Sphinkie/Radial-V/External Hardware/Carte Sparkfun FM/README.md

SparkFun FM Tuner Basic Breakout - Si4703
========================================

SparkFun FM Tuner Basic Breakout - Si4703

[*SparkFun FM Tuner Basic Breakout - Si4703 (BOB-11083)*](https://www.sparkfun.com/products/11083)

This breakout for the Silicon Laboratories Si4703 FM tuner chip is a little more stripped down than our FM Tuner Evaluation Board. 
 If your project already has an amplifier and just needs a full-featured FM tuner, this is the board for you. 

Repository Contents
-------------------

* **/SparkFunSi4703Demo**- Example code (no library required)
* **/Hardware** - Eagle design files (.brd, .sch)
* **/Libraries** - Libraries for use with the shield
* **/Production** - Production panel files (.brd)

Documentation
--------------
* **[Library](https://github.com/sparkfun/SparkFun_Si4703_Arduino_Library)** - Arduino library for the Si4703.
* **[SparkFun Fritzing repo](https://github.com/sparkfun/Fritzing_Parts)** - Fritzing diagrams for Sparkfun products.
* **[SparkFun 3D Model repo](https://github.com/sparkfun/3D_Models)** - 3D models of Sparkfun products. 

| **L OUT** | **R OUT** | **GND** | **VCC** | **SDIO** | **SCLK** | **SEN\*** | **RST\*** | **GPIO1** | **GPIO2** |
| --- | --- | --- | --- | --- | --- | --- | --- | --- | --- |
| audio | audio | ground  | 3,3 volts | bus I2C  | bus I2C  | N/U | Reset | N/U | info STC  |

License Information
-------------------

This product is _**open source**_! 

The **hardware** is released under [Creative Commons ShareAlike 4.0 International](https://creativecommons.org/licenses/by-sa/4.0/).

The **code** is beerware; if you see me (or any other SparkFun employee) at the local, and you've found our code helpful, please buy us a round!

Please use, reuse, and modify these files as you see fit. Please maintain attribution to SparkFun Electronics and release anything derivative under the same license.

Distributed as-is; no warranty is given.

- Your friends at SparkFun.
