Sphinkie/Radial-V/External Hardware/Carte ecran TFT/readme.md

# Arduino LCD Screen  (RETIRED)

## Overview

The Arduino TFT screen is a backlit LCD screen with headers. You can draw text, images, and shapes to the screen with the [TFT library](https://www.arduino.cc/en/Reference/TFTLibrary). There is an onboard micro-SD card slot on the back of the screen that  can, among other things, store bitmap images for the screen to display.

The screen's headers are designed to fit into the socket of any AVR-based Arduino (Uno, Leonardo, etc) or with the Arduino Due, Esplora, and Robot. To connect the screen to  other Arduino boards, read the tutorial on this [link](http://arduino.cc/en/Guide/TFTtoBoards).

## Hardware

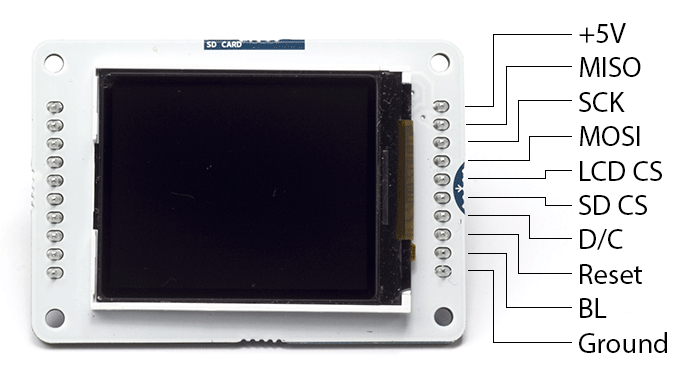
[picture p15: External Hardware/Carte ecran TFT/GLCD_pins.png]
GLCD_pins


The screen is 1.77" diagonal, with 160 x 128 pixel resolution. The  TFT library interfaces with the screen's controller through SPI when  using the [TFT library](https://www.arduino.cc/en/Reference/TFTLibrary). Refer to the [screen's data sheet](https://www.arduino.cc/en/uploads/Main/HTF0177SN-01-SPEC.pdf) for complete details.

- The screen runs on +5 VDC
- The micro-SD slot is accessible through the [SD card library](https://www.arduino.cc/en/Reference/SD).
- The LED backlight is dimmable by PWM.

## Library

The Arduino TFT library extends the [Adafruit GFX](https://github.com/adafruit/Adafruit-GFX-Library), and [Adafruit ST7735 libraries](https://github.com/adafruit/Adafruit-ST7735-Library) that it is based on. The GFX library is responsible for the drawing  routines, while the ST7735 library is specific to the screen on the  Arduino screen. The Arduino specific additions were designed to work as  similarly to the Processing API as possible.

The library is backwards compatible, which means you can still use the Adafruit functions [described here](http://learn.adafruit.com/adafruit-gfx-graphics-library/overview).

The TFT library relies on the [SPI library](https://www.arduino.cc/en/Reference/SPI), which must be included in any sketch that uses the screen.

If you wish to use the SD card, you need to include the [SD library](https://www.arduino.cc/en/Reference/SD) as well.

### Need Help?

- On the Software [on the Arduino Forum](https://forum.arduino.cc/index.php?board=63.0)

- On Projects [on the Arduino Forum](https://forum.arduino.cc/index.php?board=3.0)

- On the Product itself through [our Customer Support](https://store.arduino.cc/index.php?main_page=contact_us&language=en)

- Product Ref Code: A000096

  ## 

##
