Sphinkie/Radial-V/Hardware/Radial-V Bus/readme.md

# Radial-V

## Carte "Bus-Board"

Cette carte rassemble toutes les pins d'entrées/sorties utilisées de l'Arduino, vers une nappe 25 points, qui conduit à la carte "Extension Board". On plugge aussi dessus la carte "Sparkfun MP3 Player".

| Top View |  Bottom View |
| --- | --- |
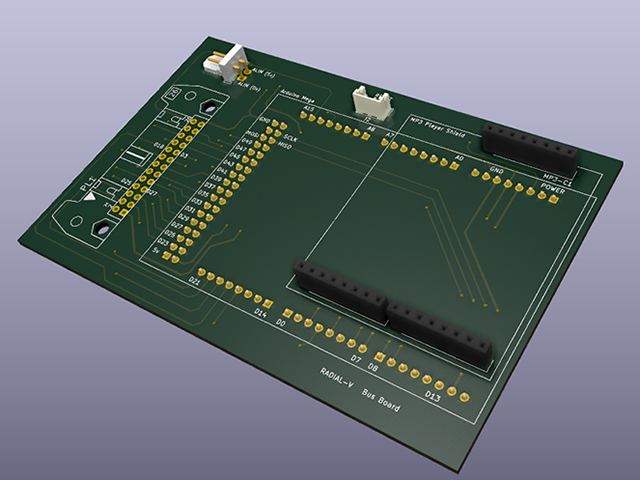
[picture p16: Hardware/Radial-V Bus/Radial-V_BusBoard-Top.png]
Radial-V Bus Board
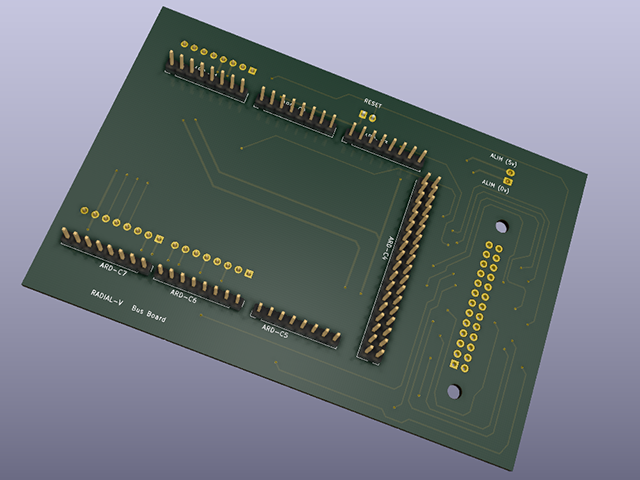
[picture p17: Hardware/Radial-V Bus/Radial-V_BusBoard-Bottom.png]
Radial-V Bus Board
|  |  |

### Schéma d'implémentation

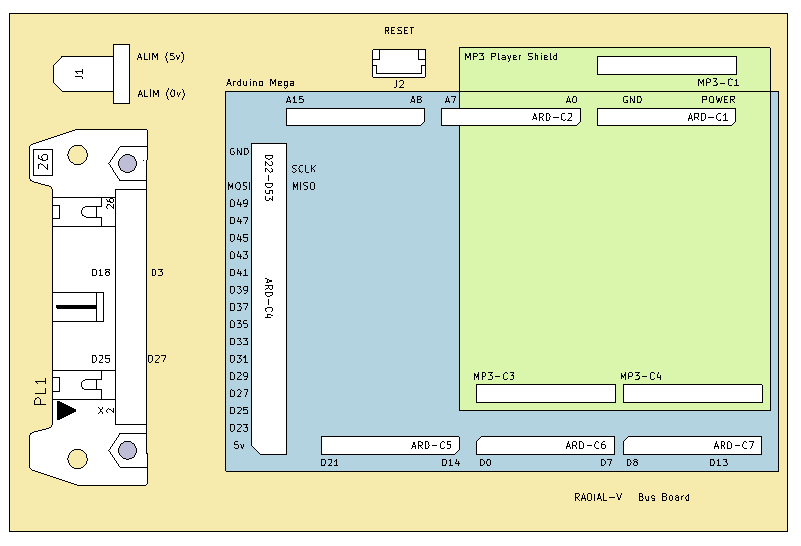
[picture p18: Hardware/Radial-V Bus/Radial-V_BusBoard-Silk.png]
Radial-V Bus Board
