Sphinkie/Radial-V/External Hardware/Carte Arduino Mega/readme.md

# RADIAL-V

## Cartes Arduino Mega

Radial-V comporte deux cartes Arduino Mega.

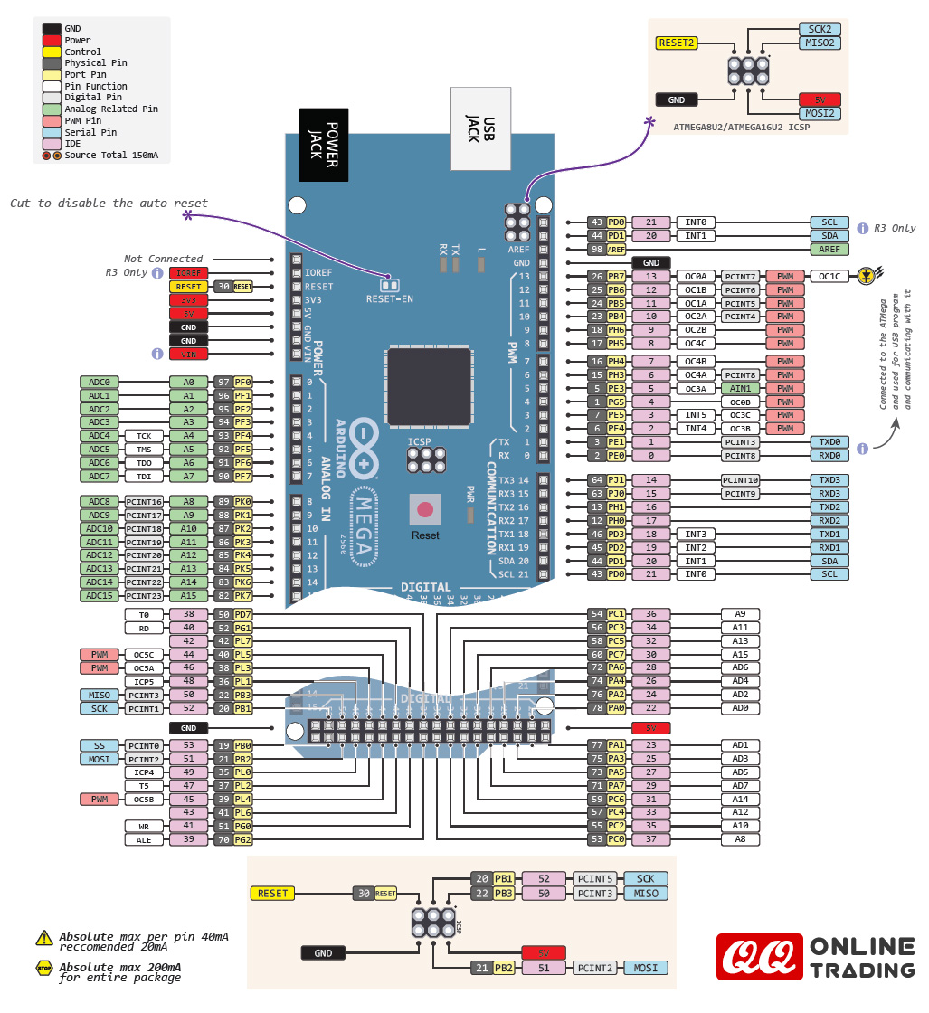
[picture p19: External Hardware/Carte Arduino Mega/Arduino_Mega_2560_Pinout.png]
Usefull Pinout


Le repository contient la documentation technique du constructeur.
