Sphinkie/Radial-V/3D objects/Boitiers/readme.md

# Radial-V

## Boîtiers

### Boîtier pour Bus Board

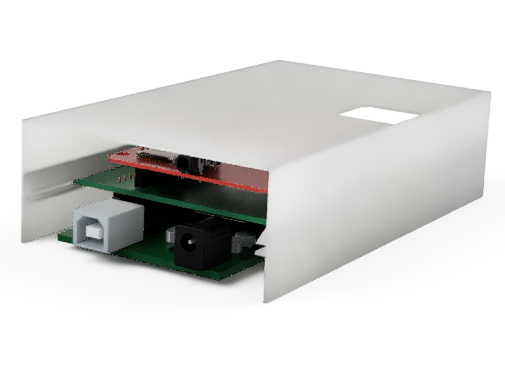
[picture p20: 3D objects/Boitiers/Couvercle_pour_Bus_Board.png]
Couvercle pour Bus Board


-----

### Boîtier pour Adaptateur Audio

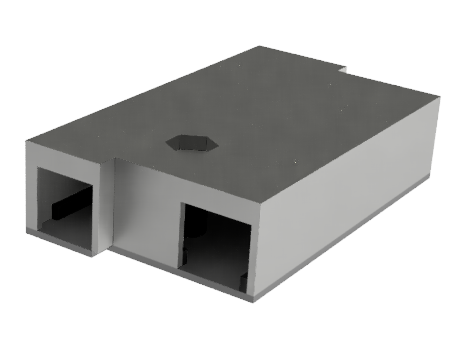
[picture p21: 3D objects/Boitiers/Boitier_Adaptateur_Audio.png]
Boitier_Adaptateur_Audio


---
