Sphinkie/Radial-V/3D objects/Support for TFT Screen Board/readme.md

# RADIAL-V

## Support pour écran TFT

Ce support permet de fixer le petit écran TFT sur le coté de la Radial-V.

[Vue du modèle 3D](Support%20for%20LCD.stl)

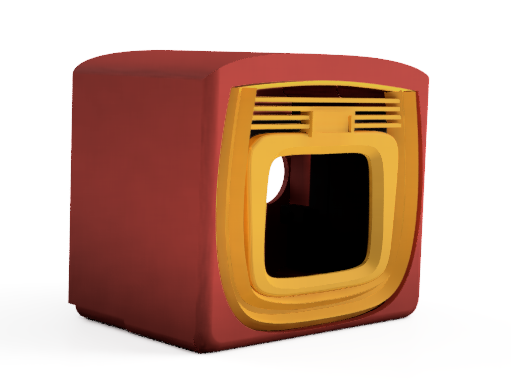
[picture p22: 3D objects/Support for TFT Screen Board/Support for LCD.png]
Vue de l'objet


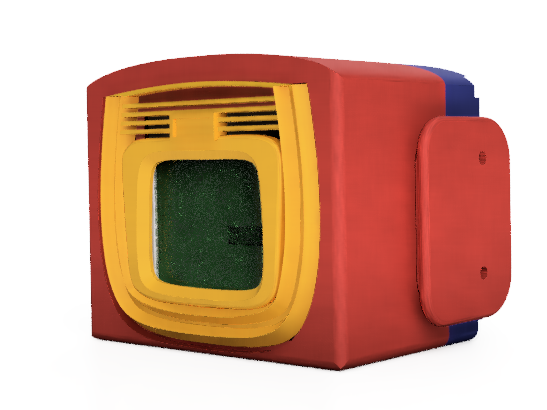
[picture p23: 3D objects/Support for TFT Screen Board/TFT_box-front.png]
TFT Box : front view


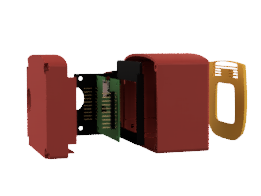
[picture p24: 3D objects/Support for TFT Screen Board/TFT_box-side.png]
TFT Box: side view
Side View:

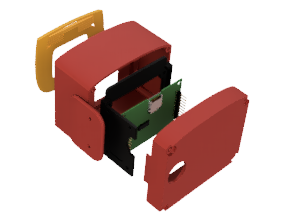
[picture p25: 3D objects/Support for TFT Screen Board/TFT_box-top.png]
TFT Box: top view
Top View:
