Sphinkie/Radial-V/3D objects/Support for Arduino Boards/readme.md

# RADIAL-V
## Supports

Ces supports permettent de rigidifier les plaques qui supportent les Arduino.
Elles se placent à chaque angle de ces plaques.

[Vue du modèle 3D](files/Radial-V%20Angles%20%28barre%20ARD1%29.stl)
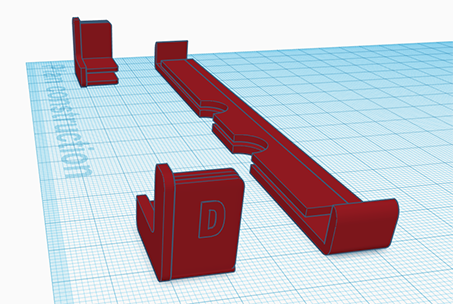
[picture p26: 3D objects/Support for Arduino Boards/images/Radial-V Angles (ARD1).png]
Exemple
