Sphinkie/Radial-V/3D objects/Support for LED/readme.md

# RADIAL-V
## Support for LED

La LED de l'activité de la carte SD a besoin d'un petit système de fixation pour se greffer au Radial-V.

[Vue du modèle 3D](Radial-V-Fixation-LED.stl)

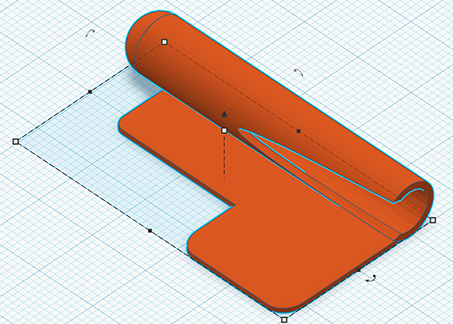
[picture p27: 3D objects/Support for LED/Radial-V-Fixation-LED.png]
Vue de l'objet
