Sphinkie/Radial-V/3D objects/Support for Extension Board/readme.md

# RADIAL-V

## Support for Extension Board

Ce support permet de fixer la carte d'extension **Ext. Board** au chassis du Radial-V.

[Vue du modèle 3D](Support_pour_Extension_Board.stl)

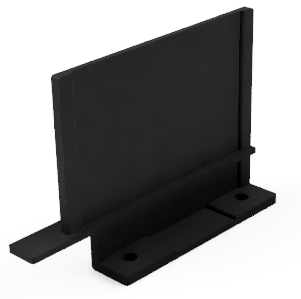
[picture p28: 3D objects/Support for Extension Board/Support_pour_Extension_Board.png]
Support_pour_Extension_Board
