Sphinkie/Radial-V/3D objects/Support for LCD Board/readme.md

# RADIAL-V

## Support pour LCD Board

Ce support permet de fixer le petit éran LCD sur le coté de la Radial-V.

[Vue du modèle 3D](Support%20for%20LCD.stl)

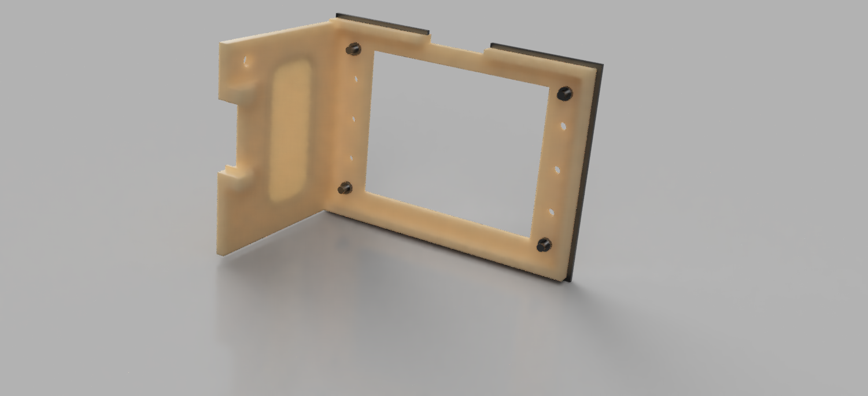
[picture p29: 3D objects/Support for LCD Board/Support for LCD.png]
Vue de l'objet
