Sphinkie/Radial-V/3D objects/Support for Alim Board/readme.md

# RADIAL-V
## Support pour la carte Alimentation

Support pour fixer la carte **Alim board** au chassis Radial-V.

[Vue du modèle 3D](Radial-V-ALIM.BOARD-Support.stl)

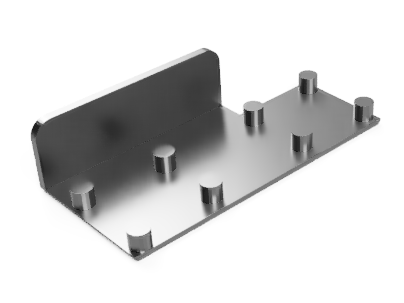
[picture p30: 3D objects/Support for Alim Board/Radial-V-ALIM.BOARD-Support_Naked.png]
Vue du support nu


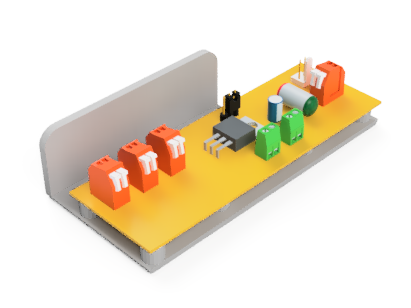
[picture p31: 3D objects/Support for Alim Board/Radial-V-ALIM.BOARD-Support_Boarded.png]
Vue du support avec la carte
