Sphinkie/Radial-V/3D objects/Support for Audio Board/readme.md

# RADIAL-V
## Support pour la carte Audio

Support pour fixer la carte **Audio Board** au chassis Radial-V.

[Vue du modèle 3D](Support%20Audio%20Board.stl)

Vue du support nu:

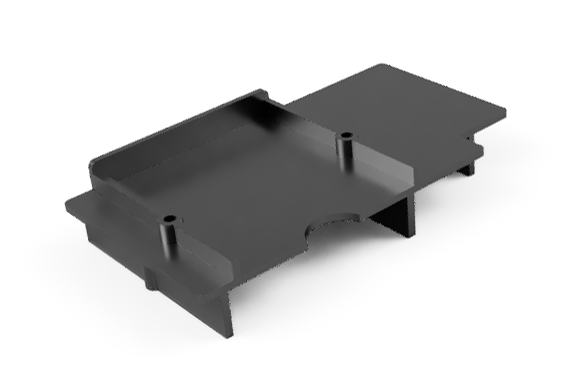
[picture p32: 3D objects/Support for Audio Board/Support_Audio_Board_naked.png]
Vue du support nu


Vue du support avec les cartes:

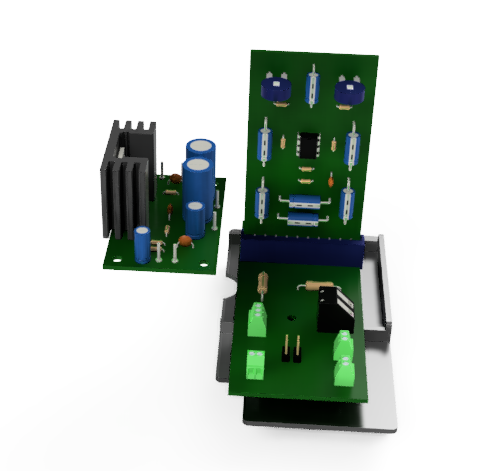
[picture p33: 3D objects/Support for Audio Board/Support_Audio_Board_boarded.png]
Vue du support avec les cartes
