Sphinkie/Radial-V/Hardware/Radial-V Audio board/3D Model/readme.md

# RADIAL-V
## Audio Board

Cette carte fait passer le signal audio par le potentiomètre de volume et l’amplificateur.

*Un slot est prévu pour un préamplificateur, qui au final ne s'est pas avéré nécessaire.*

[Vue du modèle 3D](Radial-V-Audio-Board.stl)

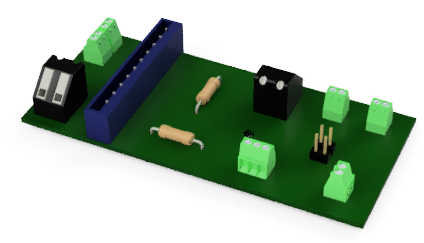
[picture p34: Hardware/Radial-V Audio board/3D Model/Radial-V-Audio-Board.png]
Vue de la carte
