Sphinkie/Radial-V/Hardware/Radial-V Extension board/3D Model/readme.md

# RADIAL-V
## Extension Board

Cette carte comporte des connecteurs d’entrée/sortie pour les différents capteurs de l’Arduino (boutons, Leds, ...)  avec leurs adaptations, et pilote les relais pour la sélection de l'audio (audio issue de la carte MP3 ou de la carte Radio-FM).

[Vue du modèle 3D](Radial-V%20Extension%20Board.stl)

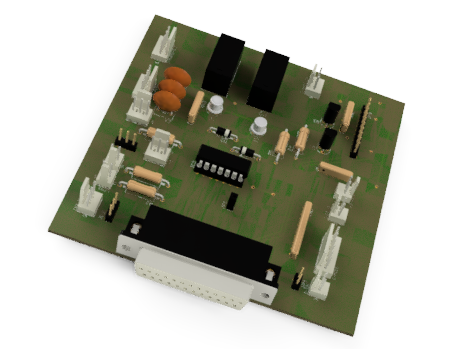
[picture p35: Hardware/Radial-V Extension board/3D Model/Radial-V_Extension_Board.png]
Vue de la carte
