Sphinkie/Radial-V/External Hardware/Carte ecran TFT/3D Model/readme.md

# RADIAL-V

## Arduino LCD Board

LCD screen with SD card for information display.

[Vue du modele 3D](Arduino_LCD_Board.stl)

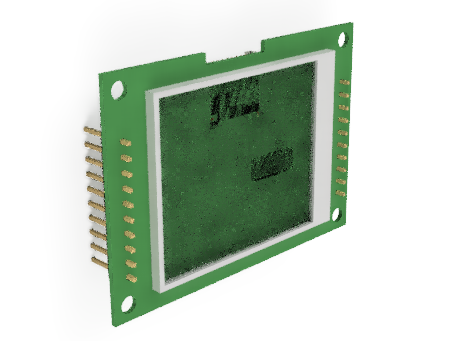
[picture p36: External Hardware/Carte ecran TFT/3D Model/Arduino_LCD_Board.png]
Arduino_LCD_Board
