Sphinkie/Radial-V/Hardware/Radial-V Alimentation board/3D Model/readme.md

# RADIAL-V
## Alimentation Board

Cette carte est alimentée par l’alimentation générale. Elle répartit l’alimentation vers les différents composants:
* Carte Arduino Master (5v)
* Carte Arduino Slave (5v)
* Carte Audio Board: Pré-Ampli et Ampli (12v)
* Lampes de la face avant (5v)

[Vue du modèle 3D](Radial-V-AlimBoard.stl)

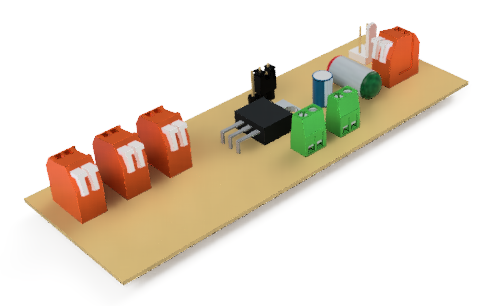
[picture p38: Hardware/Radial-V Alimentation board/3D Model/Radial-V-AlimBoard-02.png]
Vue de la carte
