Sphinkie/Radial-V/External Hardware/Carte Amplifier VM114/3D Model/readme.md

# RADIAL-V

## 3D model : Amplifier Board

Amplificateur audio mono 4W.

[Vue du modèle 3D](Velleman_Amplifier_VM114.stl)

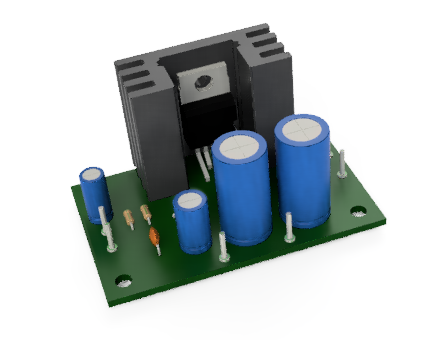
[picture p39: External Hardware/Carte Amplifier VM114/3D Model/Velleman_Amplifier_VM114.png]
Vue de la carte
