Sphinkie/Radial-V/External Hardware/Carte Arduino Mega/3D Model/readme.md

# RADIAL-V
## 3D model: Arduino Mega

Le système comporte deux cartes Arduino Mega: ARD1 (Master) et ARD2 (Slave).

* ARD1: utilise 19 I/O (dont 6 avec interruption) ce qui nécessite un Mega.
* ARD2: consomme 2 à 3 kB de RAM, ce qui nécessite un Mega.

Les deux Arduino communiquent en I2C.

[Vue du modèle 3D](ArduinoMega2560.stl)

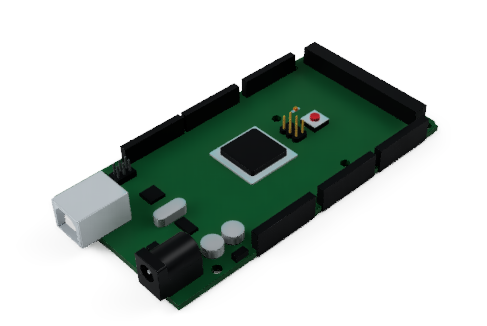
[picture p40: External Hardware/Carte Arduino Mega/3D Model/ArduinoMega2560.png]
Vue de la carte
