Sphinkie/Radial-V/External Hardware/Carte Sparkfun MP3 Player Shield/Sparkfun Repository/MP3_Player_Shield-V_1.3/README.MD

MP3 Player Shield
==================

[MP3 Player Shield  
*MP3 Player Shield (DEV-10628)*](https://www.sparkfun.com/products/10628)

The MP3 Player Shield has a microSD socket, VS1053 decoder IC and all the supporting circuitry to be able to decode and play MP3s from an Arduino.

Repository Contents
-------------------
* **/Firmware** - Multiple examples of how to read MP3 files and send them to the VS1053.
* **/Hardware** - All Eagle design files (.brd, .sch)

License Information
-------------------

The hardware is released under [Creative Commons Share-alike 3.0](http://creativecommons.org/licenses/by-sa/3.0/).  

All other code is open source so please feel free to do anything you want with it; you buy me a beer if you use this and we meet someday ([Beerware license](http://en.wikipedia.org/wiki/Beerware)).
