Sphinkie/Radial-V/3D objects/Boitiers/Boitier Adapter Capa.png

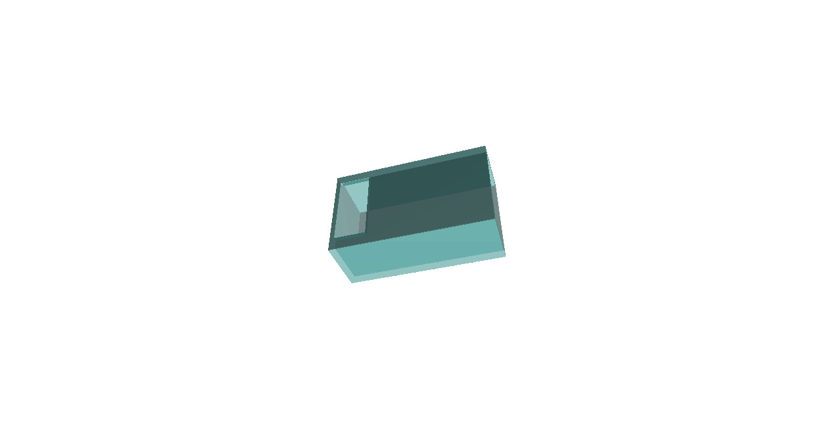
3D objects/Boitiers/Boitier Adapter Capa.png
