Sphinkie/Radial-V/3D objects/Boitiers/Couvercle Adaptateur Audio.png

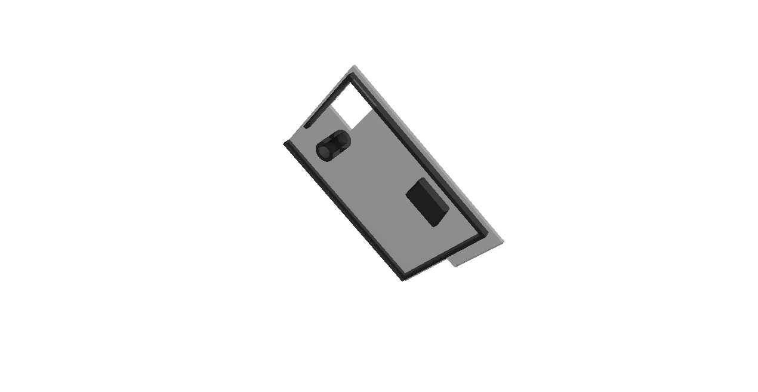
3D objects/Boitiers/Couvercle Adaptateur Audio.png
