Sphinkie/Radial-V/3D objects/Boitiers/Support for Amplifier.png

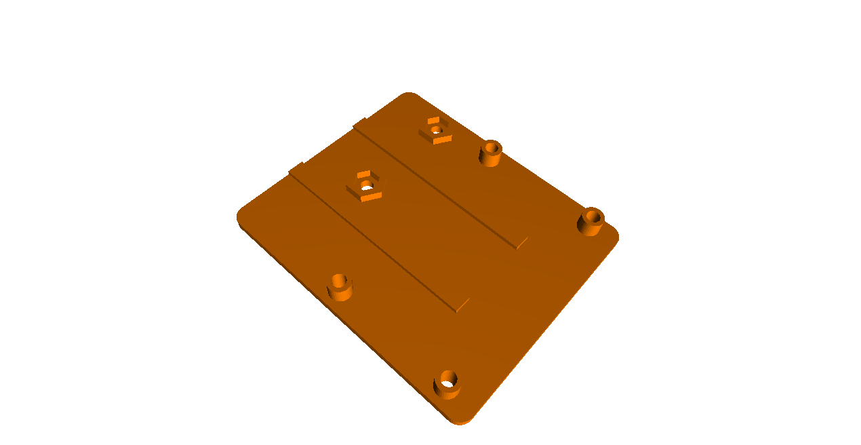
3D objects/Boitiers/Support for Amplifier.png
