Sphinkie/Radial-V/3D objects/Support for Arduino Boards/images/Angles.jpg

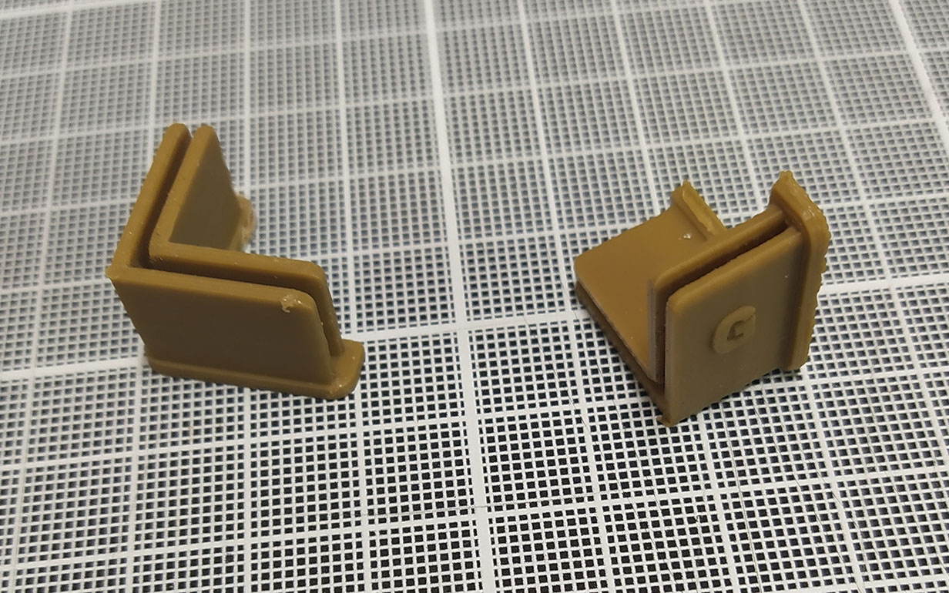
3D objects/Support for Arduino Boards/images/Angles.jpg
