Sphinkie/Radial-V/3D objects/Support for Arduino Boards/images/Barre-ARD1.jpg

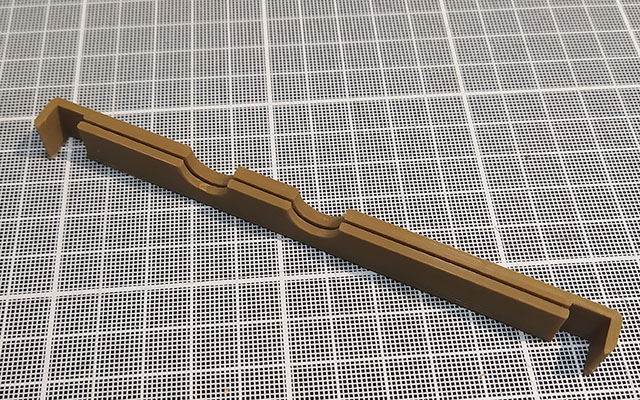
3D objects/Support for Arduino Boards/images/Barre-ARD1.jpg
