Sphinkie/Radial-V/3D objects/Support for Arduino Boards/images/Barre.jpg

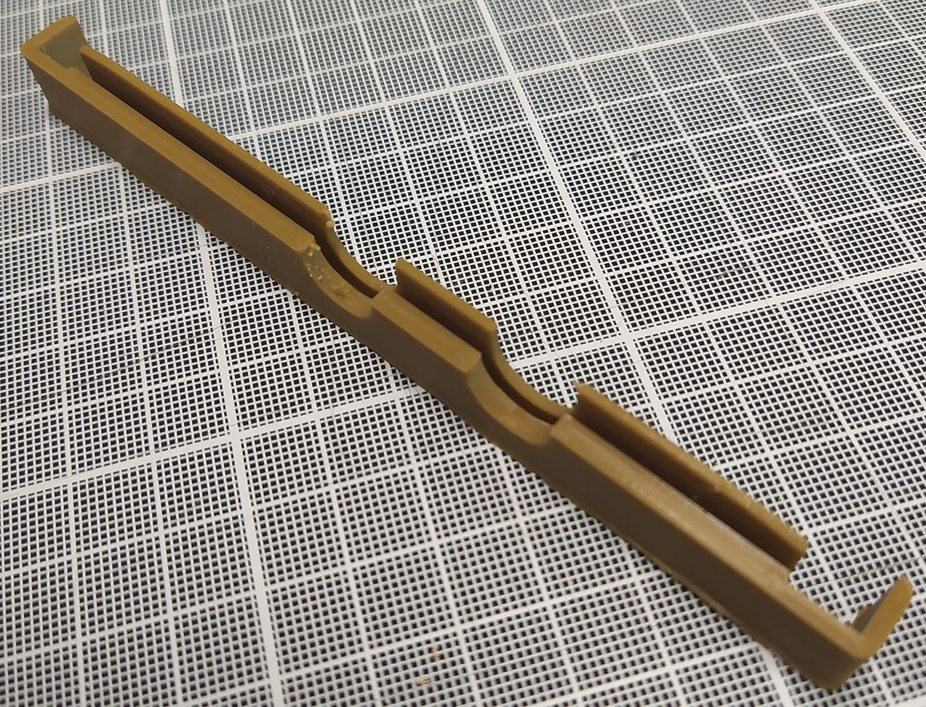
3D objects/Support for Arduino Boards/images/Barre.jpg
