Sphinkie/Radial-V/3D objects/Support for Arduino Boards/images/Radial-V Angles (barre ARD1).png

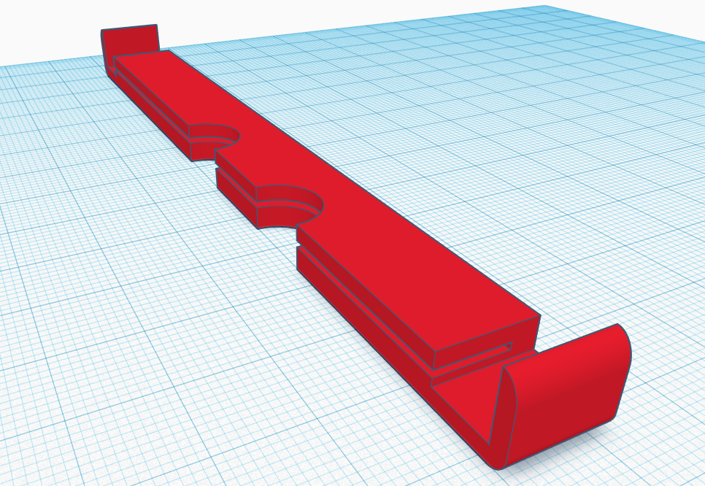
3D objects/Support for Arduino Boards/images/Radial-V Angles (barre ARD1).png
