Sphinkie/Radial-V/3D objects/Support for Arduino Boards/images/Radial-V Angles (coins ARD2).png

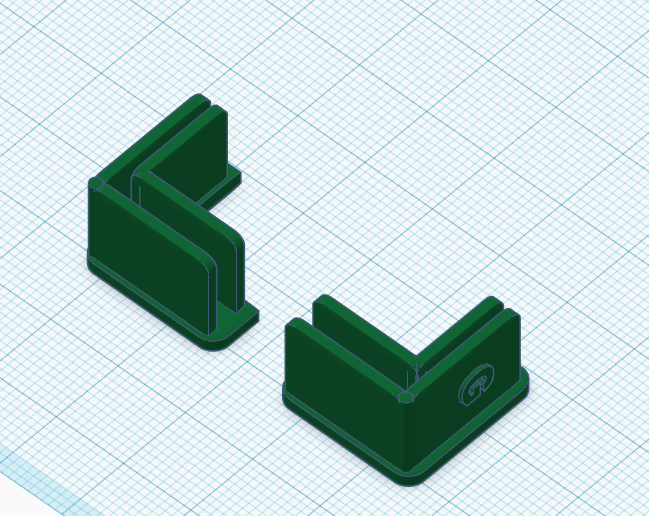
3D objects/Support for Arduino Boards/images/Radial-V Angles (coins ARD2).png
