Sphinkie/Radial-V/3D objects/Support for LED/Support-LED.jpg

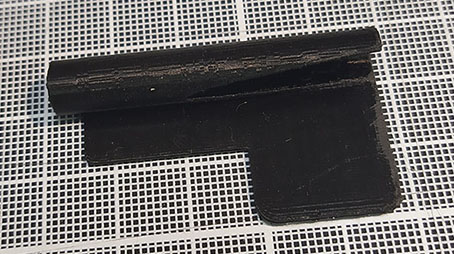
3D objects/Support for LED/Support-LED.jpg
