Sphinkie/Radial-V/docs/images/Radial-V-BeACat.png

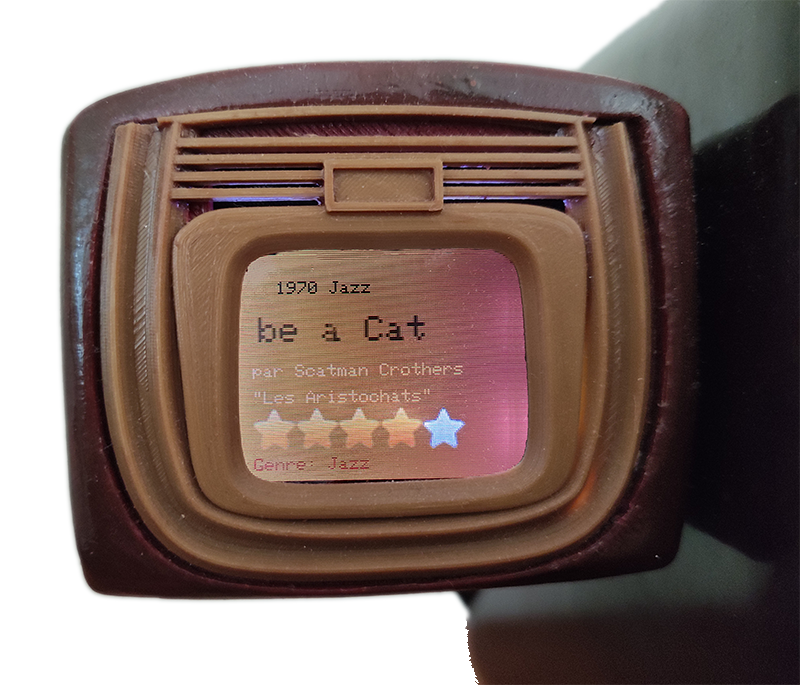
docs/images/Radial-V-BeACat.png
