Sphinkie/Radial-V/docs/images/Radial-V-frontPanel.png

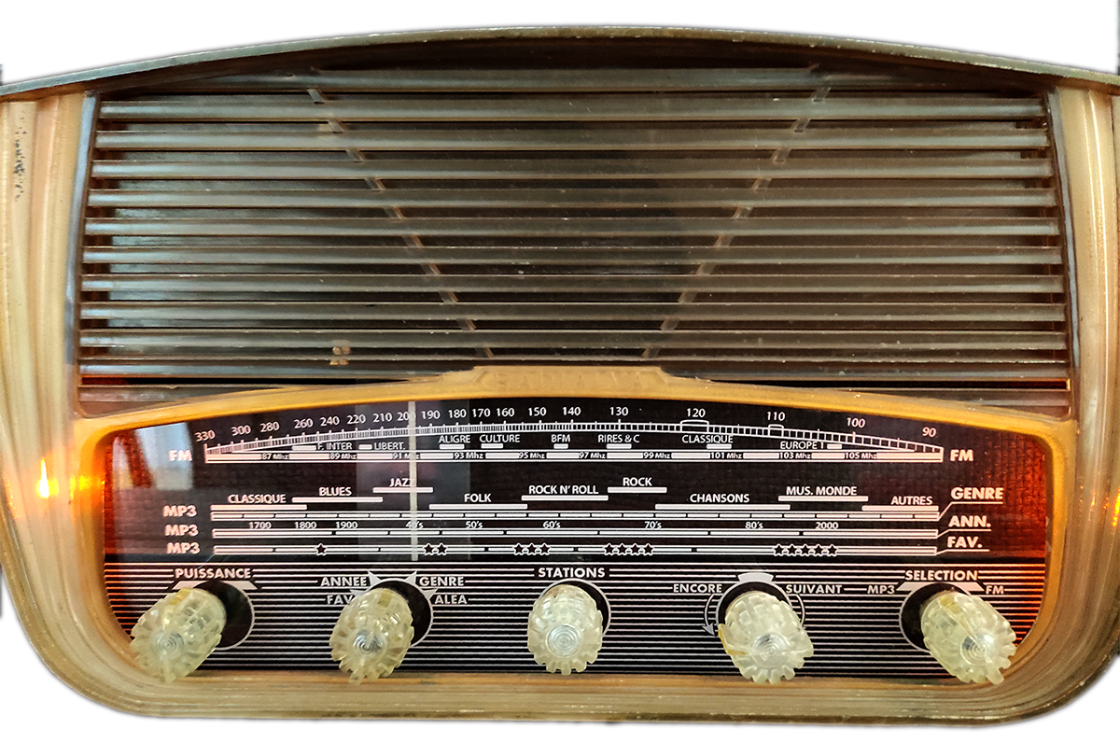
docs/images/Radial-V-frontPanel.png
