Sphinkie/Radial-V/docs/images/Radial-V-lcd.png

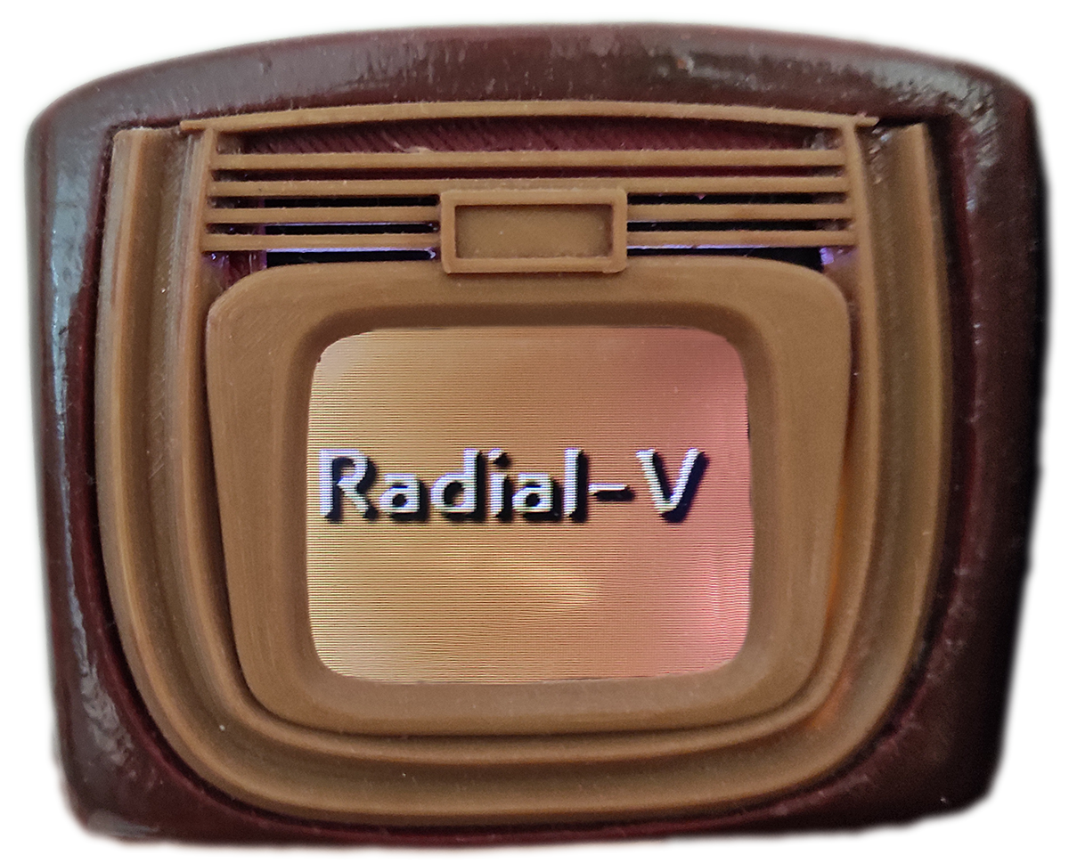
docs/images/Radial-V-lcd.png
