Sphinkie/Radial-V/docs/images/Radial-V-off-2.png

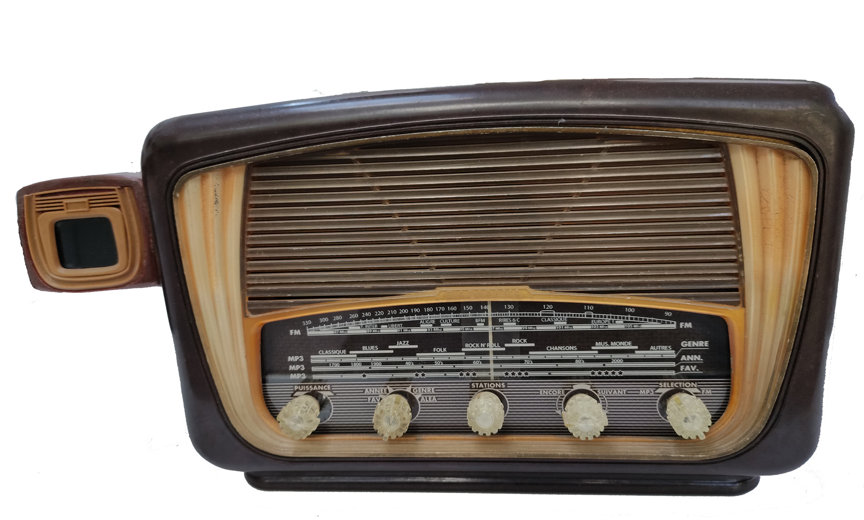
docs/images/Radial-V-off-2.png
