Sphinkie/Radial-V/docs/images/Radial-V-off-white.png

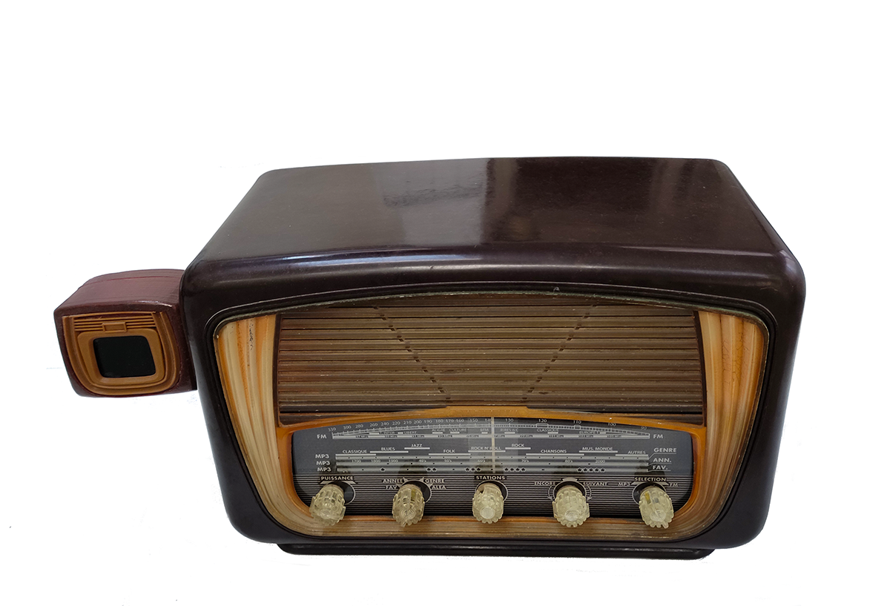
docs/images/Radial-V-off-white.png
