Sphinkie/Radial-V/docs/images/Radial-V-on-closer.png

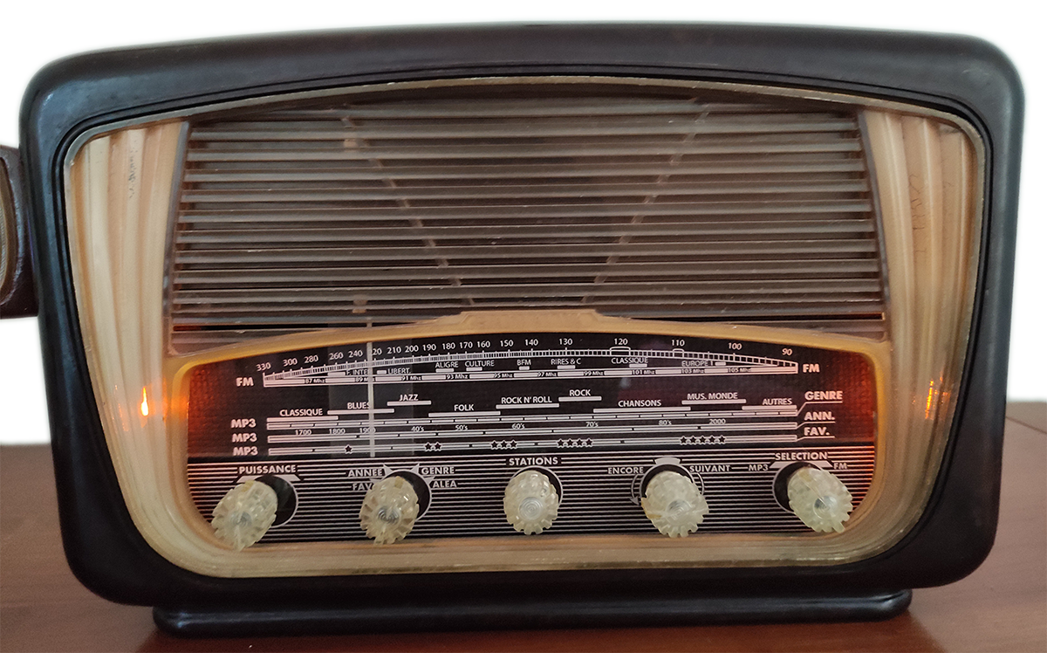
docs/images/Radial-V-on-closer.png
