Sphinkie/Radial-V/docs/images/Radial-V-withoutScreen.png

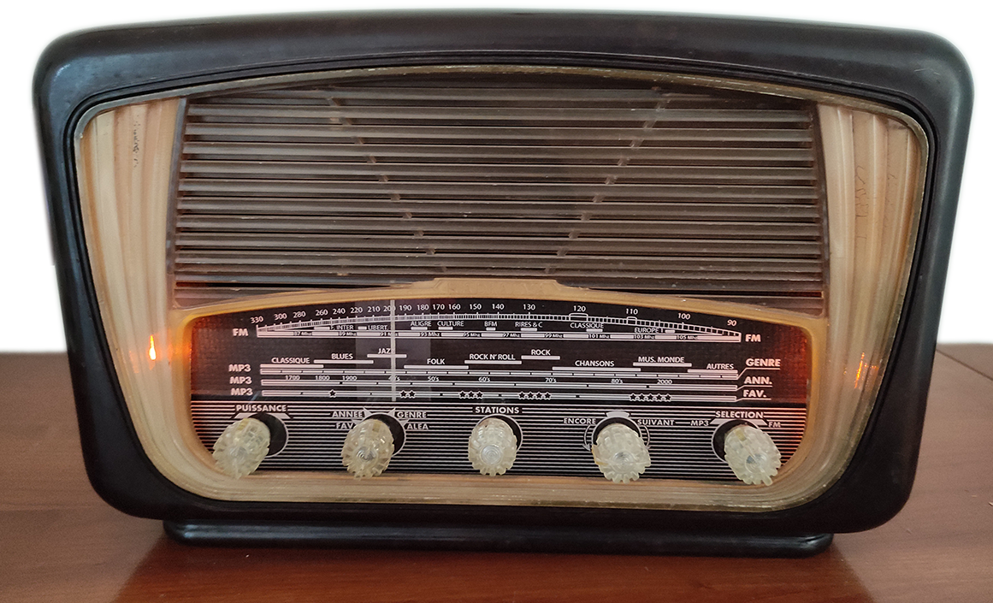
docs/images/Radial-V-withoutScreen.png
