Sphinkie/Radial-V/External Hardware/Carte Amplifier VM114/kiCad Schematics/Velleman Amplifier VM114.png

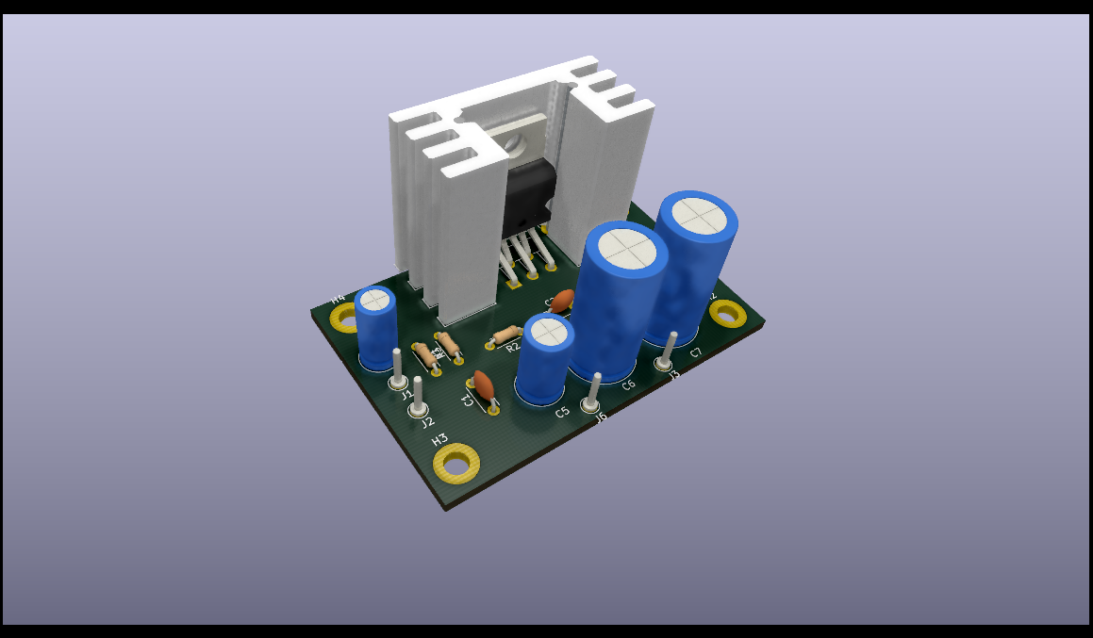
External Hardware/Carte Amplifier VM114/kiCad Schematics/Velleman Amplifier VM114.png
