Sphinkie/Radial-V/External Hardware/Carte ecran TFT/A000096_top_2.jpg

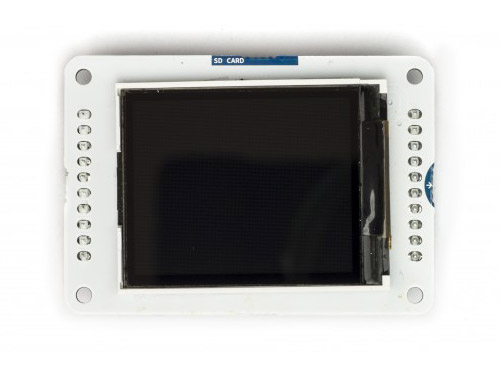
External Hardware/Carte ecran TFT/A000096_top_2.jpg
