Sphinkie/Radial-V/External Hardware/Carte ecran TFT/LCD-screen.jpg

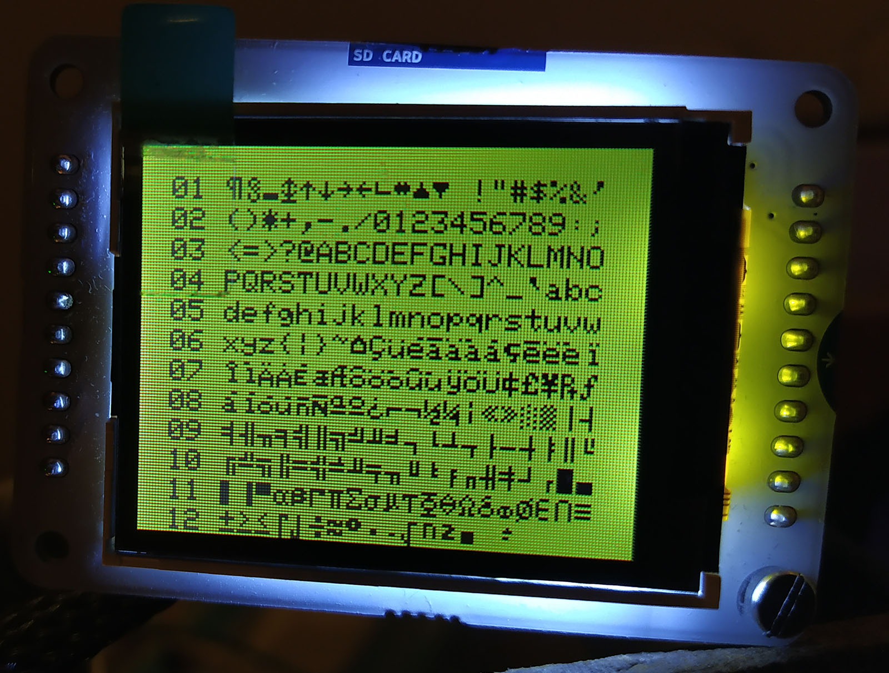
External Hardware/Carte ecran TFT/LCD-screen.jpg
