Sphinkie/Radial-V/External Hardware/Carte Sparkfun FM/Analyse I2C/Mesure 4.png

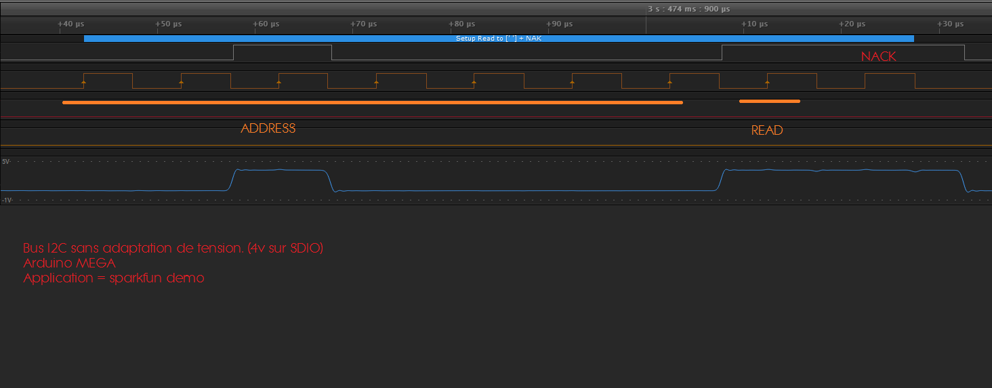
External Hardware/Carte Sparkfun FM/Analyse I2C/Mesure 4.png
