Sphinkie/Radial-V/External Hardware/Carte Sparkfun FM/Analyse I2C/Mesure ACK.png

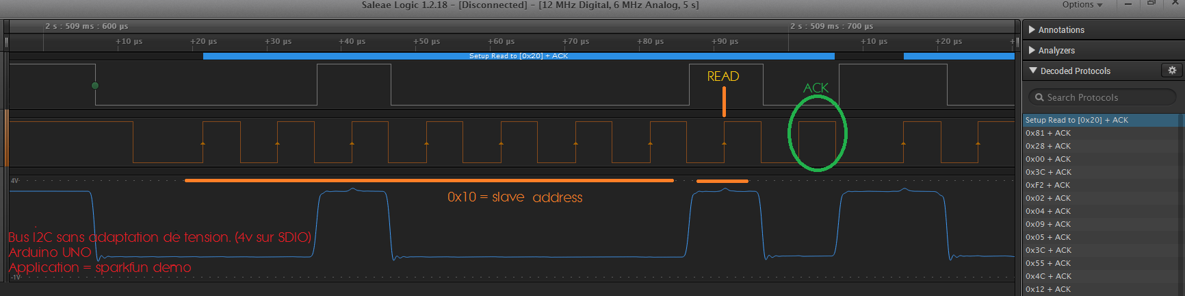
External Hardware/Carte Sparkfun FM/Analyse I2C/Mesure ACK.png
