Sphinkie/Radial-V/External Hardware/Carte Sparkfun FM/Analyse I2C/Mesure DATA.png

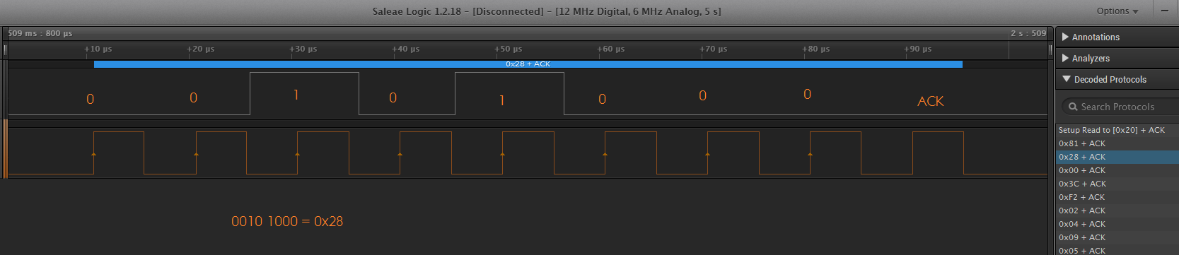
External Hardware/Carte Sparkfun FM/Analyse I2C/Mesure DATA.png
