Sphinkie/Radial-V/External Hardware/Carte Sparkfun FM/Analyse I2C/Mesure RADIALV-2.png

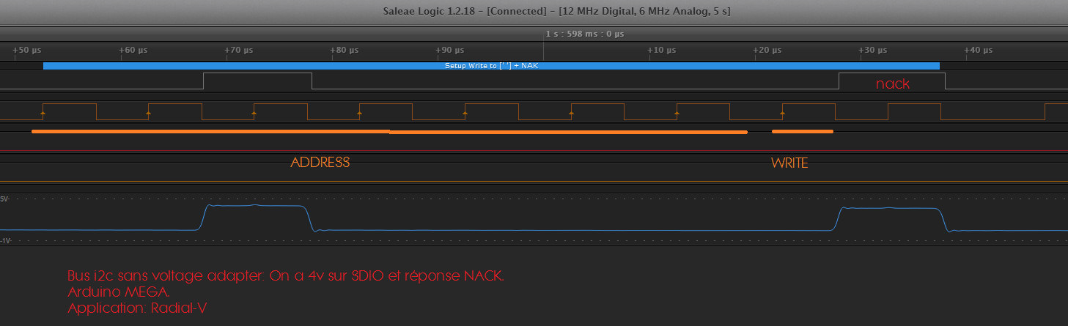
External Hardware/Carte Sparkfun FM/Analyse I2C/Mesure RADIALV-2.png
