Sphinkie/Radial-V/External Hardware/Carte Sparkfun FM/Pictures/11083-01.jpg

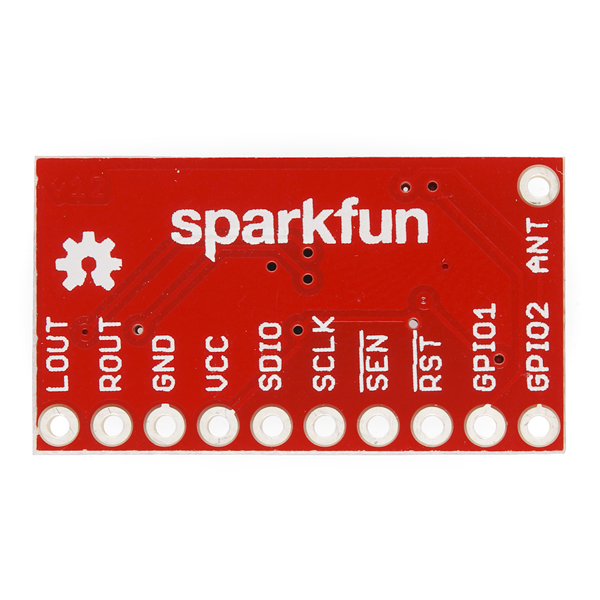
External Hardware/Carte Sparkfun FM/Pictures/11083-01.jpg
