Sphinkie/Radial-V/Hardware/Radial-V Alimentation board/3D Model/Radial-V-AlimBoard-01.png

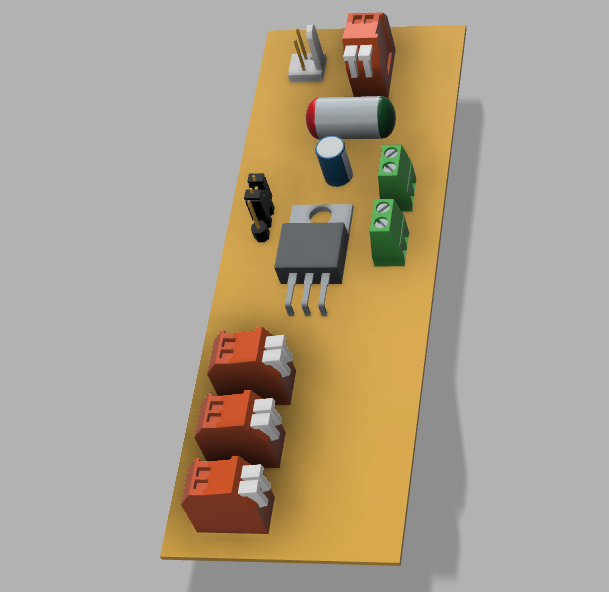
Hardware/Radial-V Alimentation board/3D Model/Radial-V-AlimBoard-01.png
