Sphinkie/Radial-V/Hardware/Radial-V Alimentation board/Radial-A Alim Schematic.png

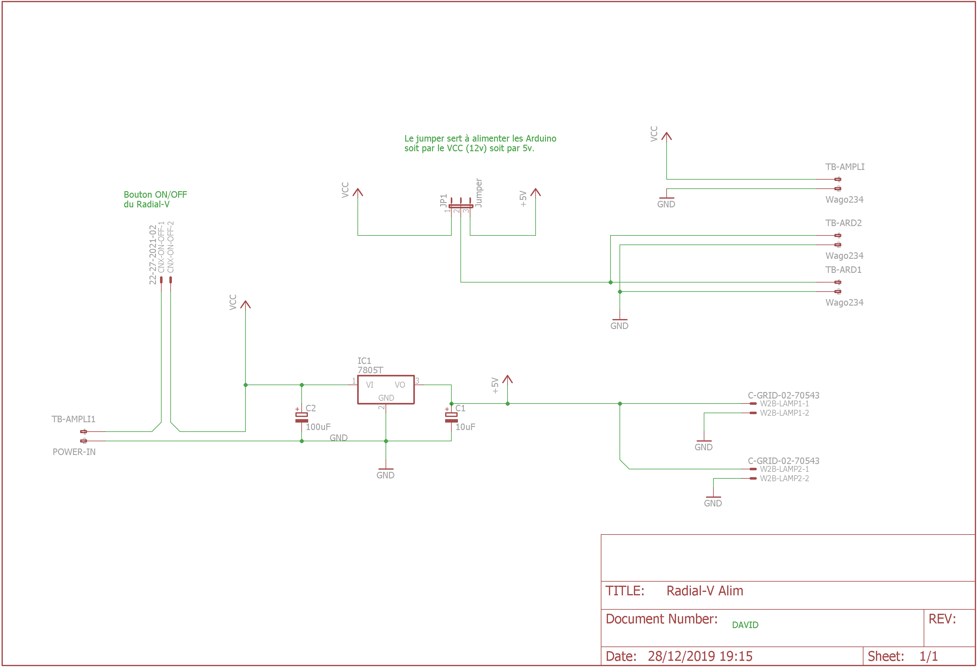
Hardware/Radial-V Alimentation board/Radial-A Alim Schematic.png
