Sphinkie/Radial-V/Hardware/Radial-V Alimentation board/Radial-V-Alim-Layer-Bottom.png

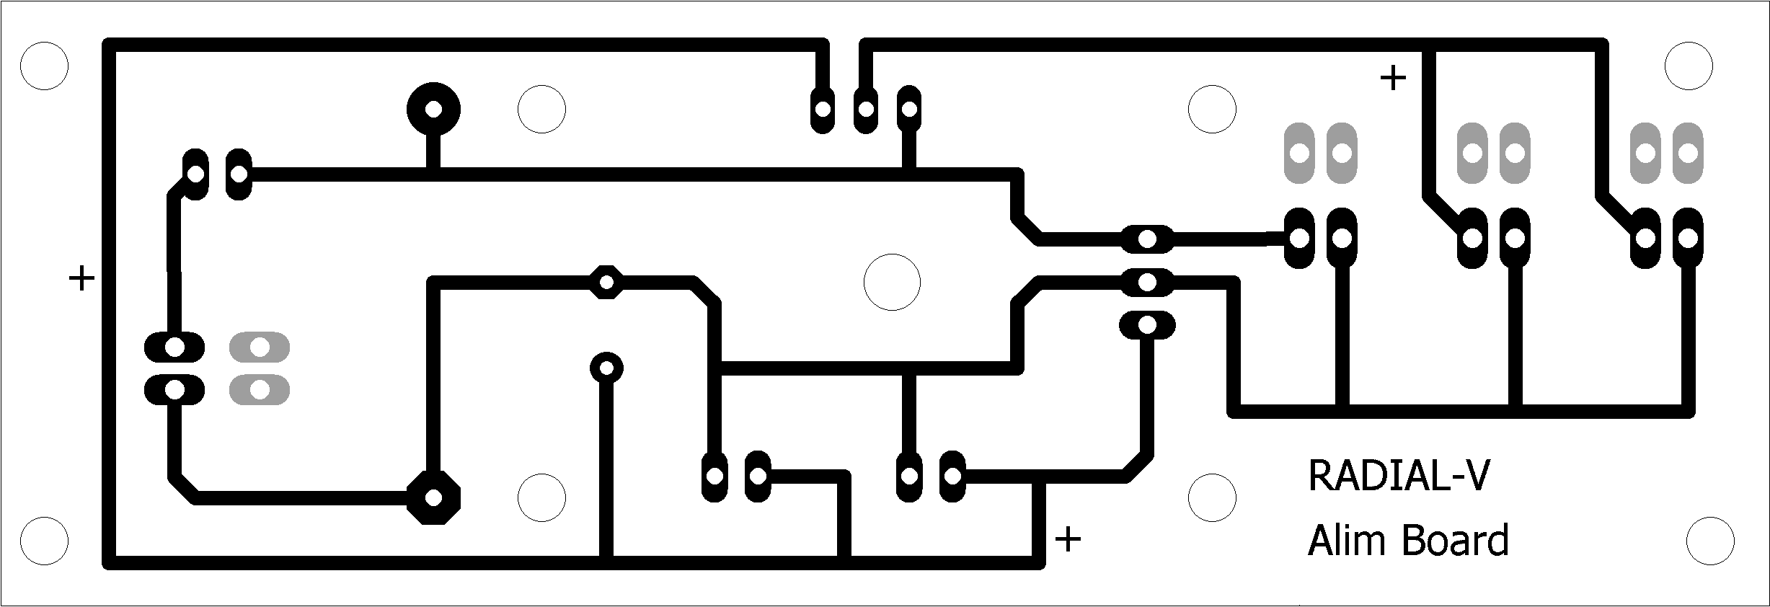
Hardware/Radial-V Alimentation board/Radial-V-Alim-Layer-Bottom.png
