Sphinkie/Radial-V/Hardware/Radial-V Alimentation board/Radial-V-Alim-Layer-Top.png

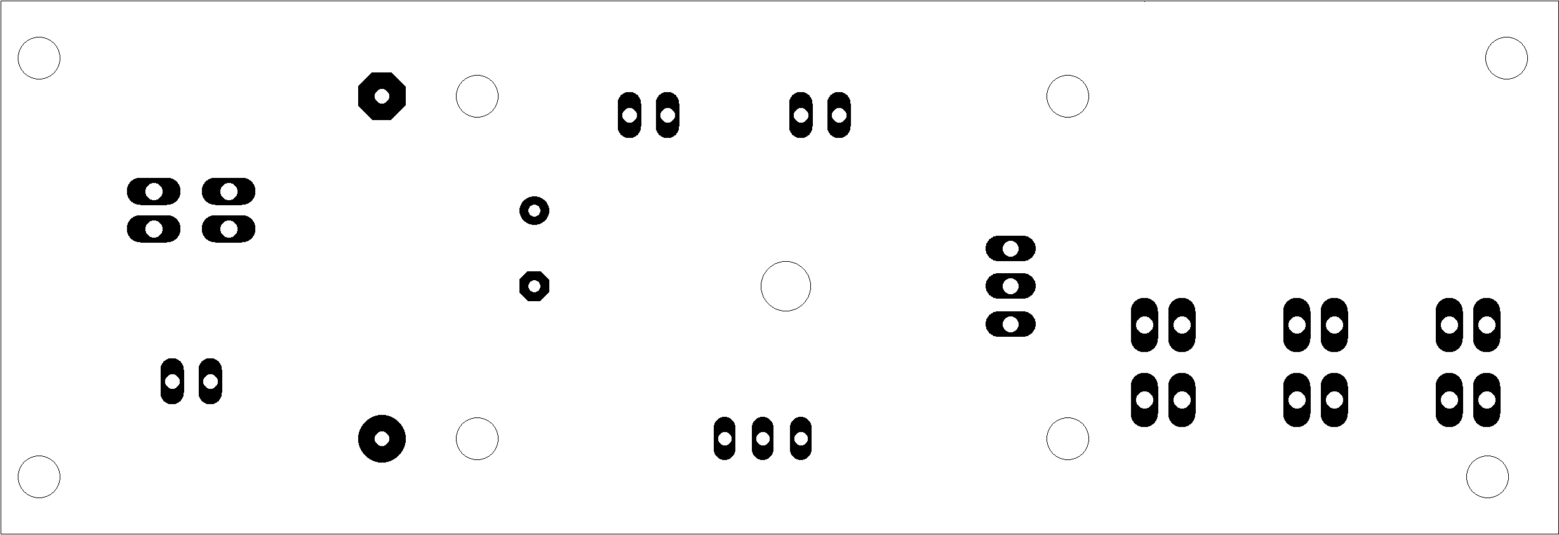
Hardware/Radial-V Alimentation board/Radial-V-Alim-Layer-Top.png
