Sphinkie/Radial-V/Hardware/Radial-V Audio board/3D Model/Radial-V-Audio-Board-1.png

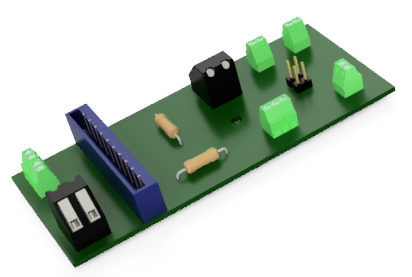
Hardware/Radial-V Audio board/3D Model/Radial-V-Audio-Board-1.png
