Sphinkie/Radial-V/Hardware/Radial-V Audio board/Radial-V_AudioBoard_01.png

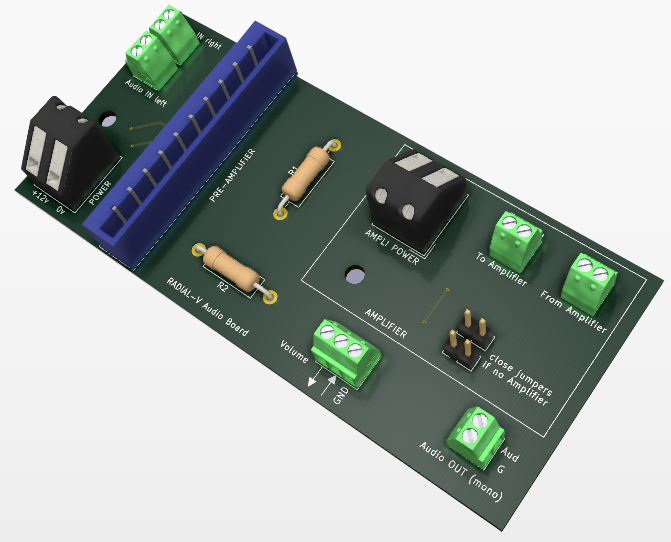
Hardware/Radial-V Audio board/Radial-V_AudioBoard_01.png
