Sphinkie/Radial-V/Hardware/Radial-V Extension board/Radial-V Extension Board Shematic p1.png

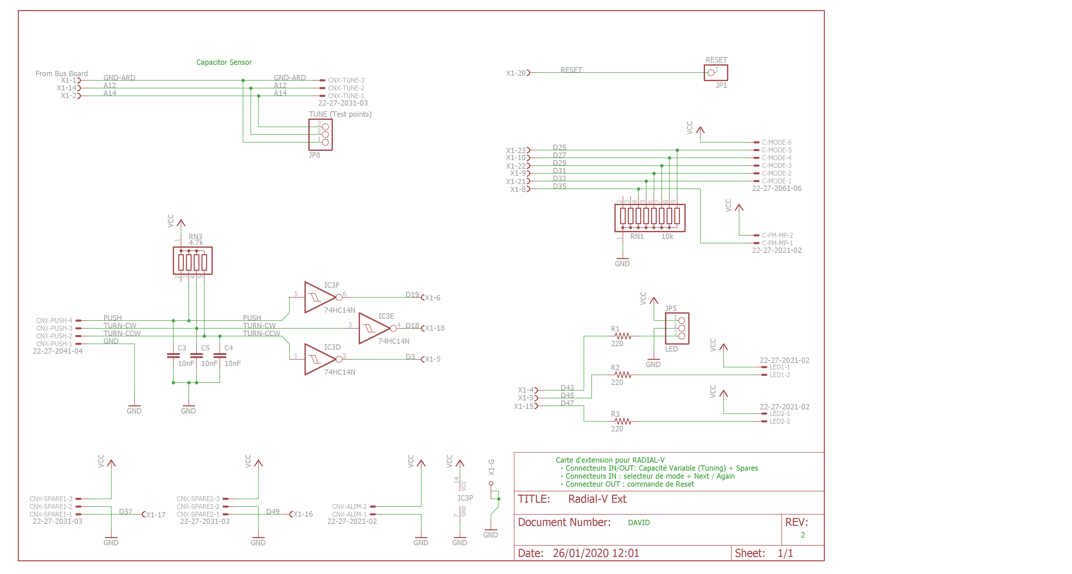
Hardware/Radial-V Extension board/Radial-V Extension Board Shematic p1.png
