Sphinkie/Radial-V/Hardware/Radial-V Extension board/Radial-V Extension Board Shematic p2.png

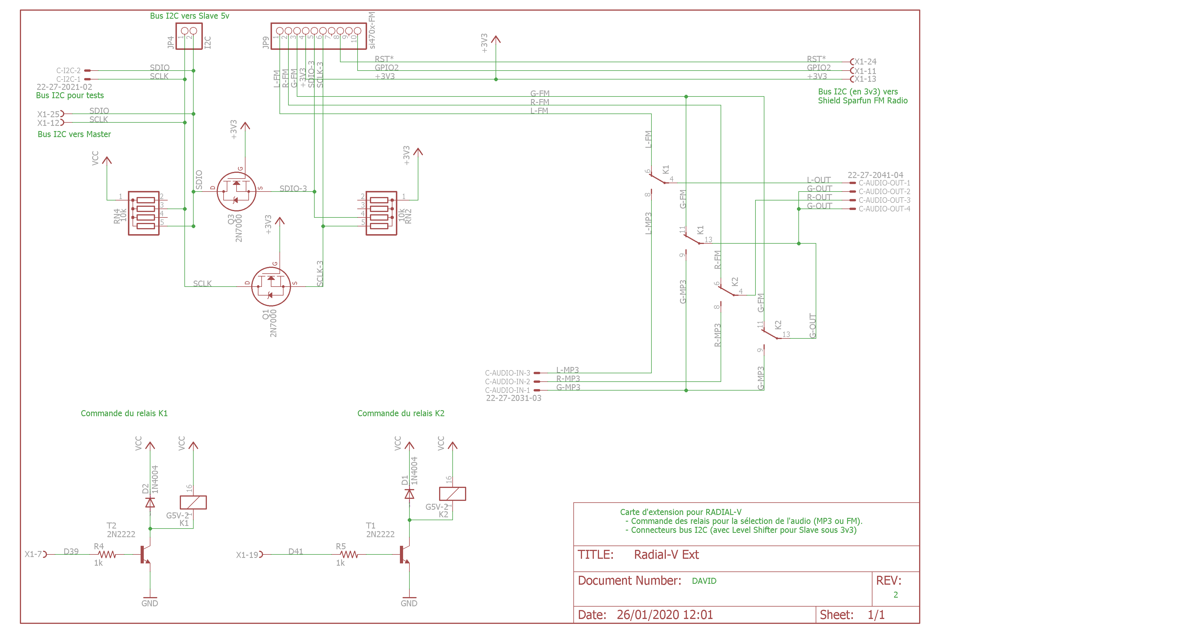
Hardware/Radial-V Extension board/Radial-V Extension Board Shematic p2.png
