Sphinkie/Radial-V/Hardware/Radial-V Extension board/Radial-V Extension Board Shematic.png

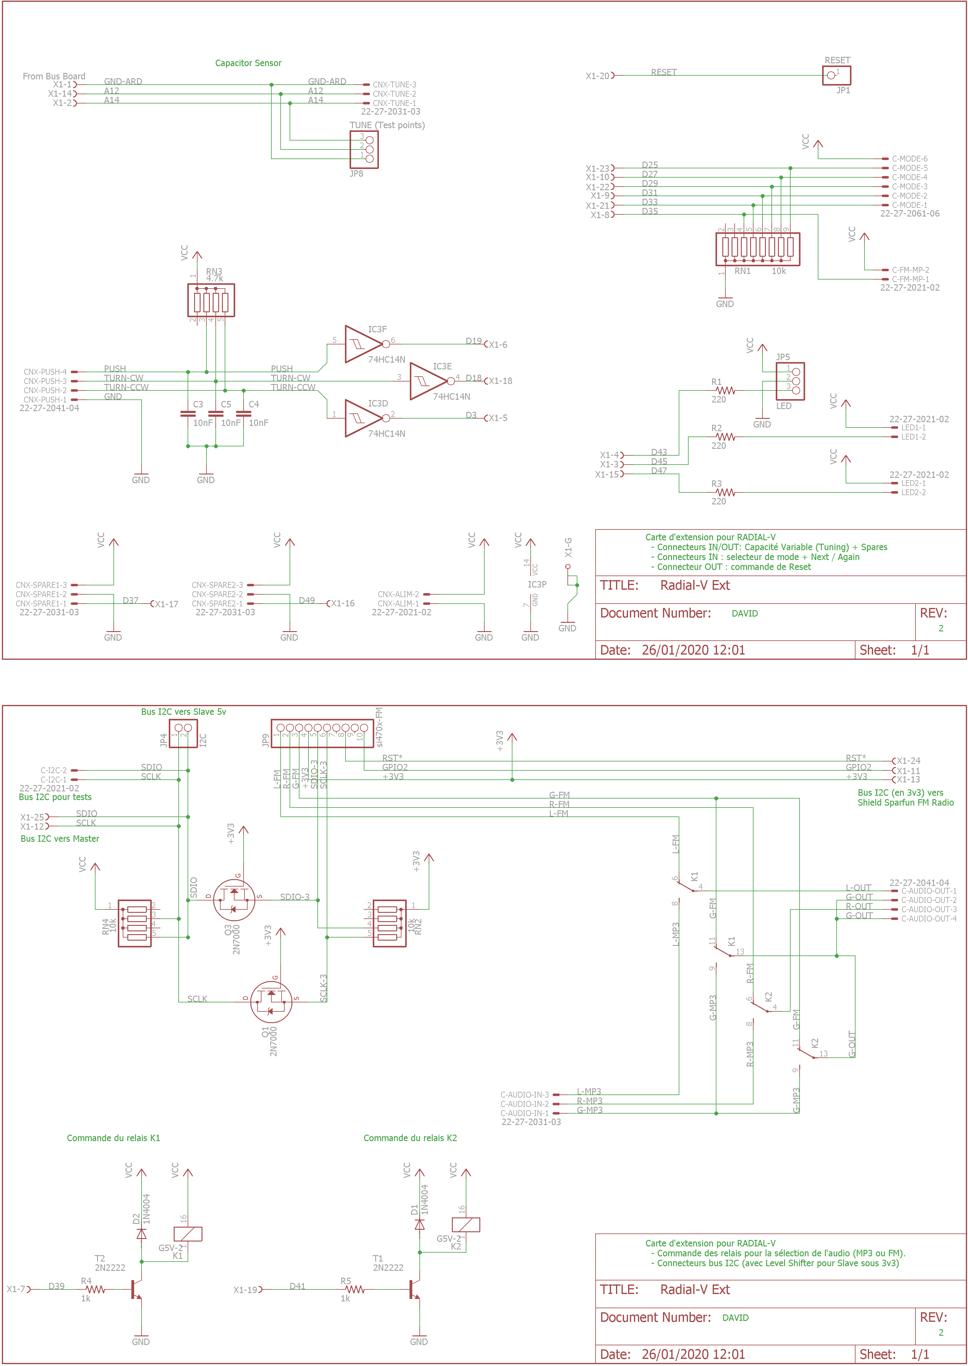
Hardware/Radial-V Extension board/Radial-V Extension Board Shematic.png
