Sphinkie/Radial-V/Hardware/Radial-V Extension board/Radial-V-Ext-Layer-Bottom.png

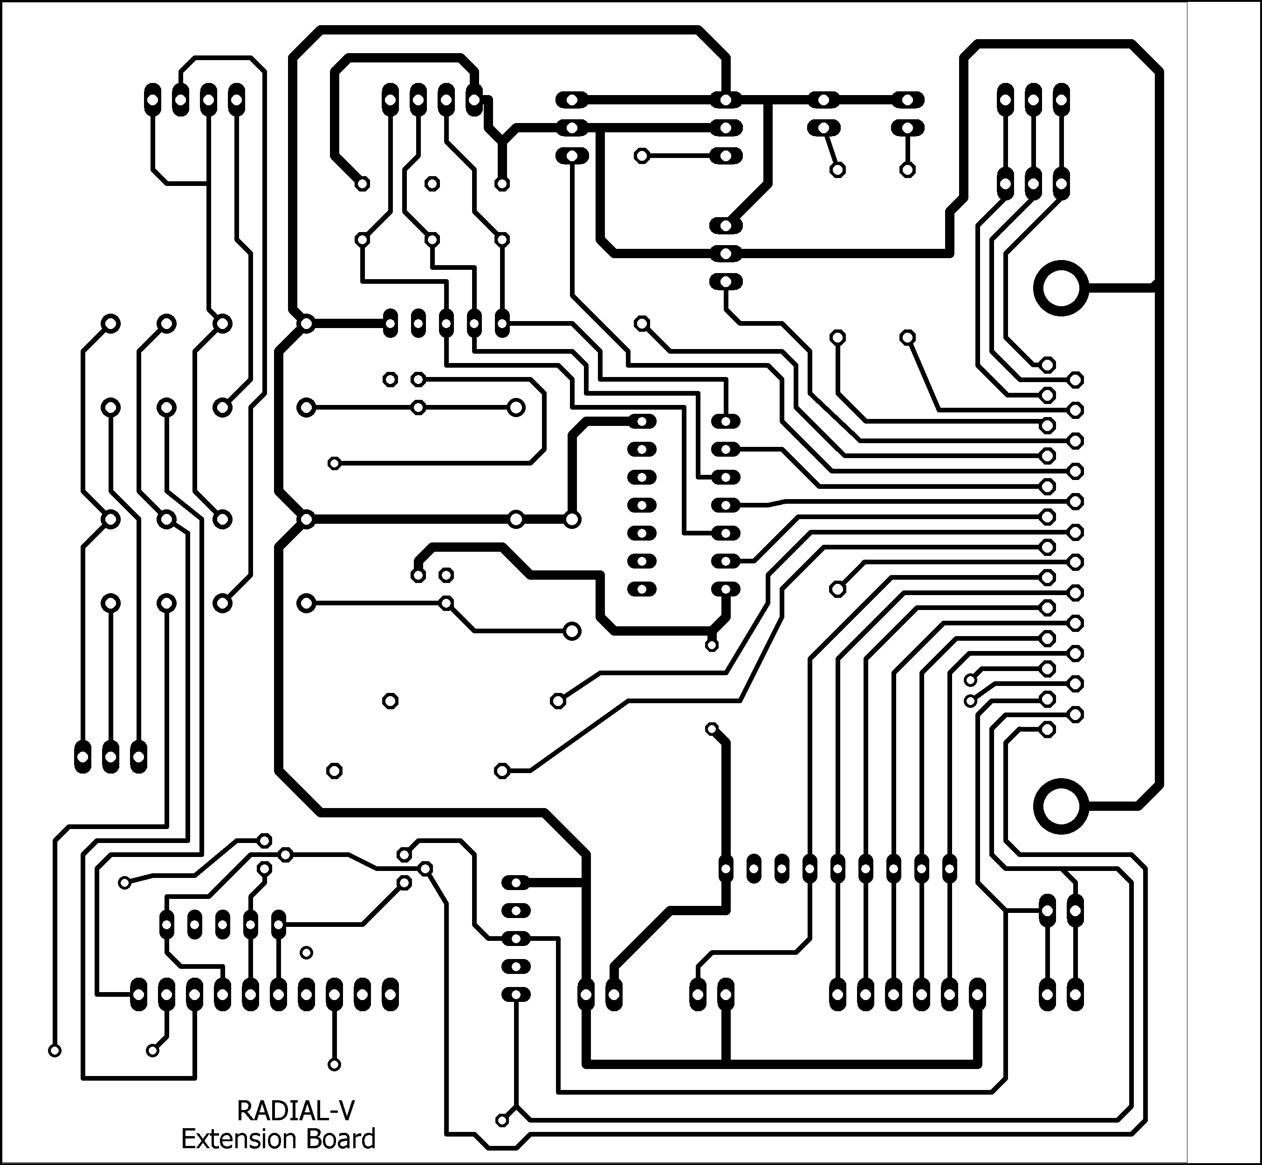
Hardware/Radial-V Extension board/Radial-V-Ext-Layer-Bottom.png
