Sphinkie/Radial-V/Hardware/Radial-V Extension board/Radial-V-Ext-Layer-Top.png

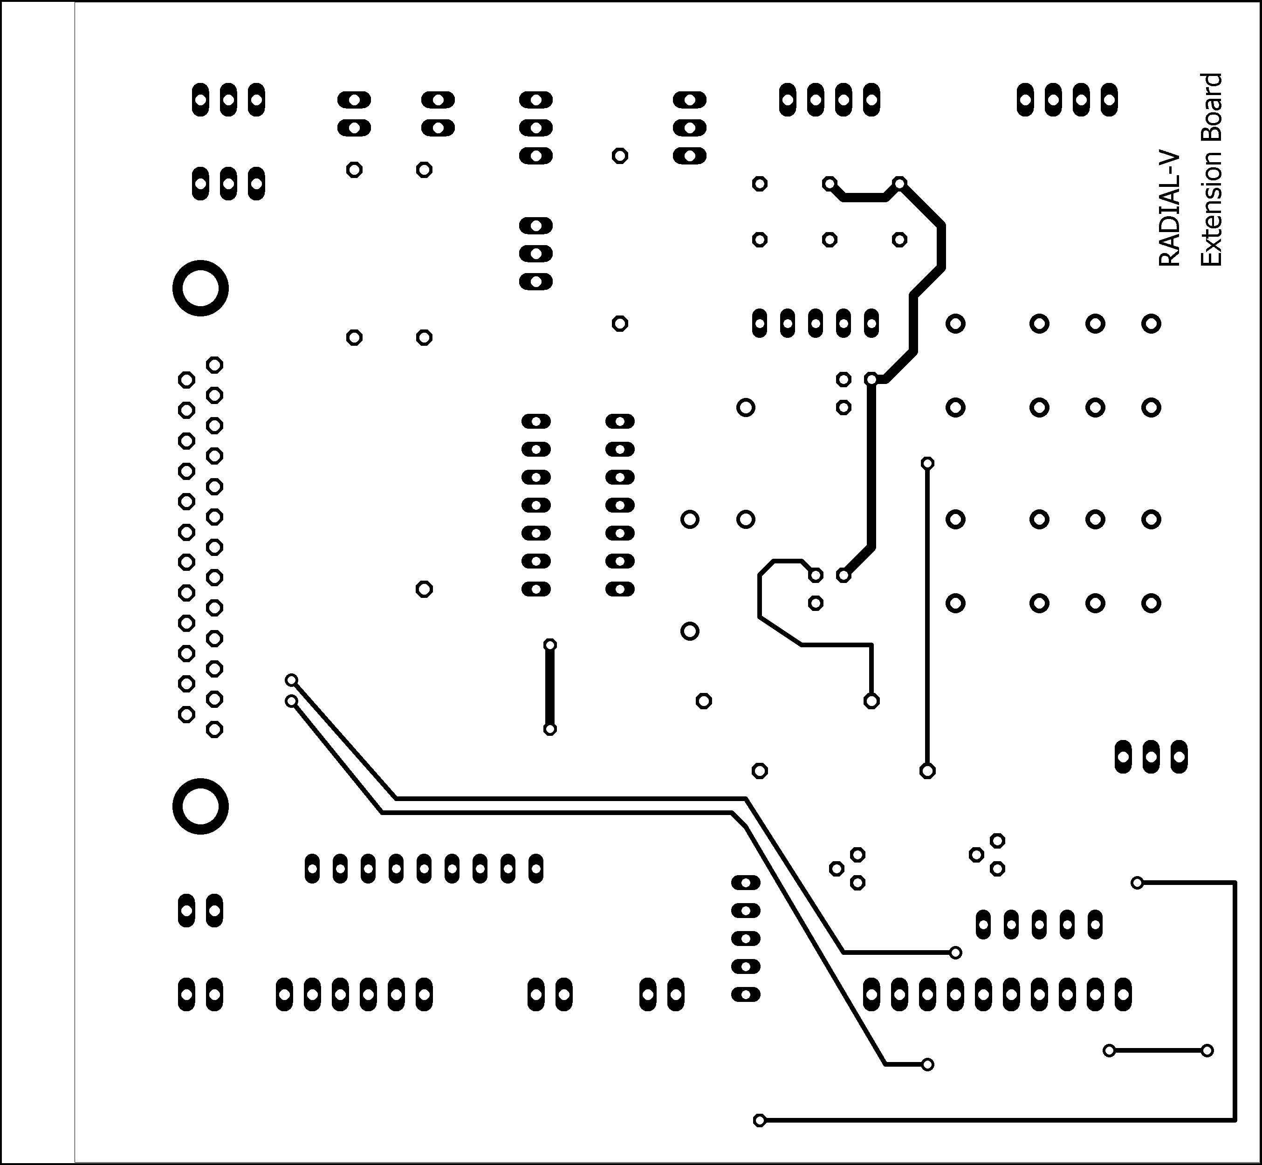
Hardware/Radial-V Extension board/Radial-V-Ext-Layer-Top.png
