Sphinkie/Radial-V/Plexiglass/Model_Photo_1.jpg

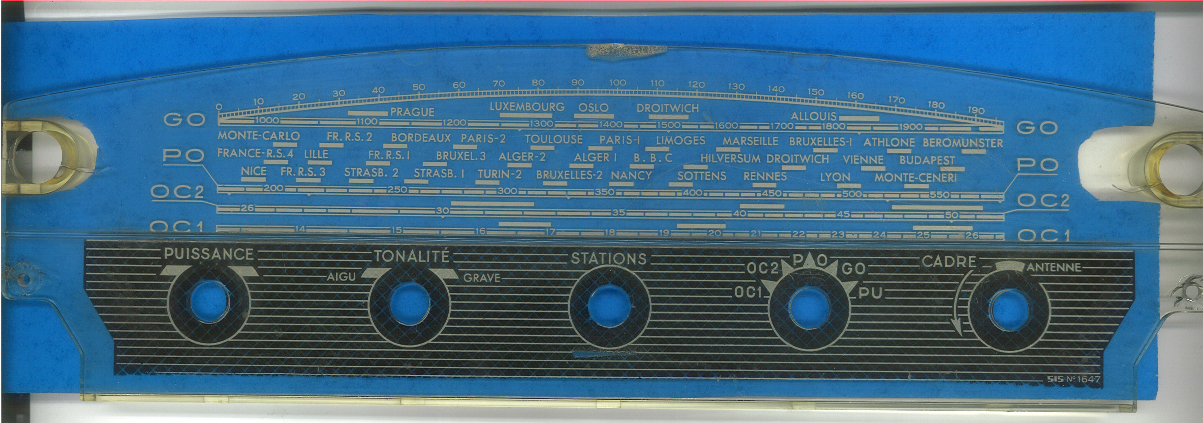
Plexiglass/Model_Photo_1.jpg
