Sphinkie/Radial-V/Plexiglass/Model_Photo_2.jpg

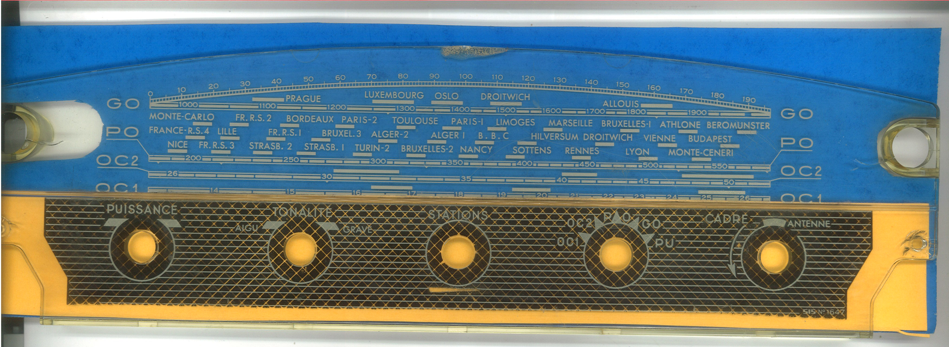
Plexiglass/Model_Photo_2.jpg
