Sphinkie/Radial-V/Plexiglass/Plexi Radialva.png

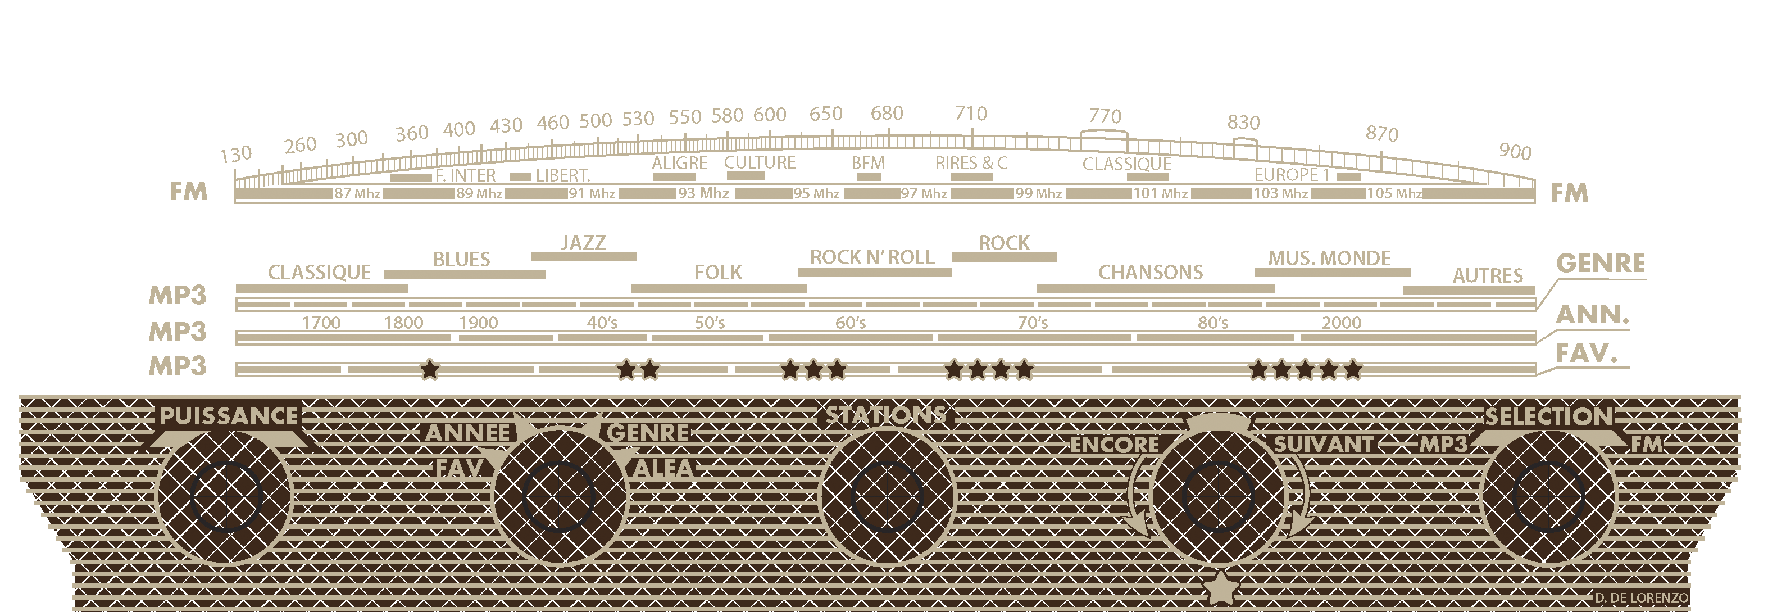
Plexiglass/Plexi Radialva.png
