Sphinkie/Radial-V/SD_card LCD/Preparation/Background/bg_FRAME.bmp

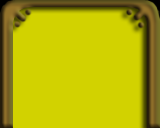
SD_card LCD/Preparation/Background/bg_FRAME.bmp
