Sphinkie/Radial-V/SD_card LCD/Preparation/Background/bg_RADV.bmp

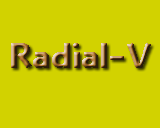
SD_card LCD/Preparation/Background/bg_RADV.bmp
