Sphinkie/Radial-V/SD_card LCD/Preparation/Background/bg_TATOO.bmp

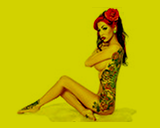
SD_card LCD/Preparation/Background/bg_TATOO.bmp
