Sphinkie/Radial-V/SD_card LCD/SD-card/bg_RADV.bmp

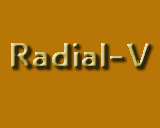
SD_card LCD/SD-card/bg_RADV.bmp
