Sphinkie/Radial-V/Hardware/Radial-V PreAmplifier Shunt/3D model/Radial-V PreAmplifier Shunt.step

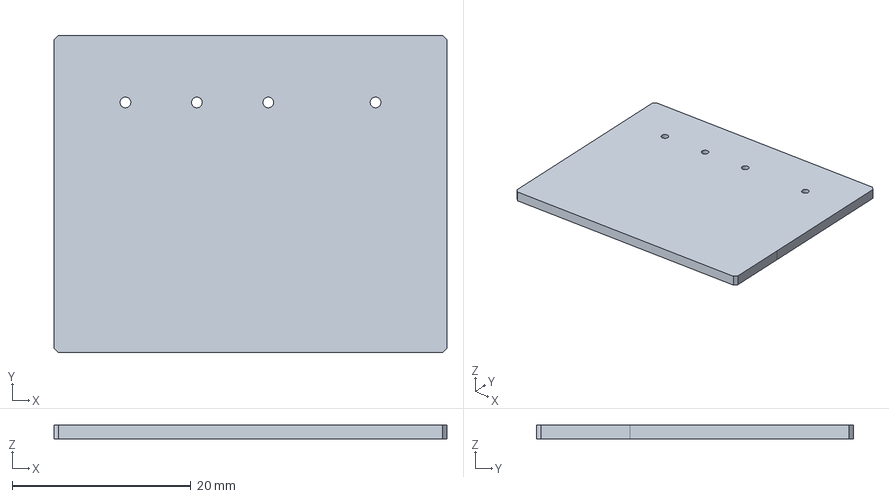
[picture p133: CAD file, 2020-04-20]
Hardware/Radial-V PreAmplifier Shunt/3D model/Radial-V PreAmplifier Shunt.step
44.0 x 35.5 x 1.60 mm
