Sphinkie/Radial-V/3D objects/Boitiers/Boitier Adapter Capa.stl

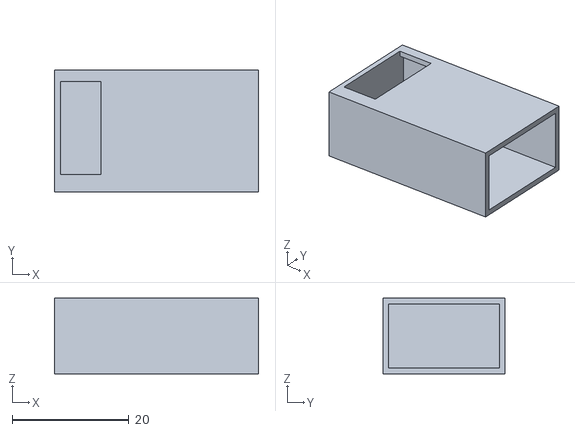
[picture p134: CAD file, 2024-02-11]
3D objects/Boitiers/Boitier Adapter Capa.stl
35.0 x 21.0 x 13.0
