Sphinkie/Radial-V/3D objects/Support for Arduino Boards/files/Radial-V Angles (barre ARD1).stl

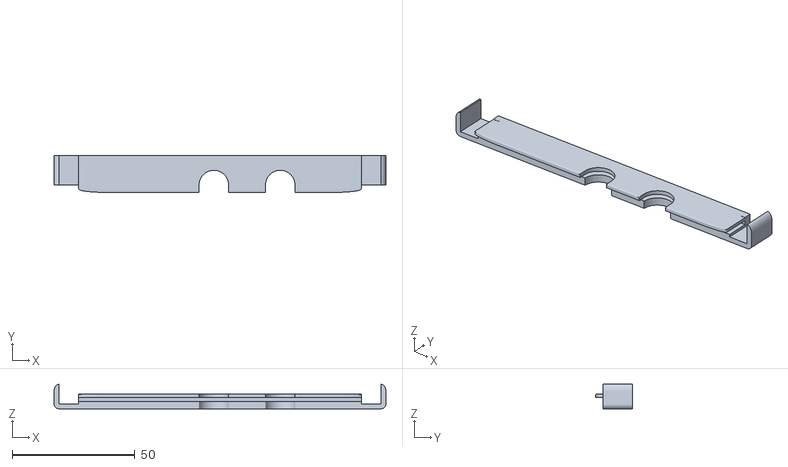
[picture p135: CAD file, 2020-01-11]
3D objects/Support for Arduino Boards/files/Radial-V Angles (barre ARD1).stl
135.0 x 15.0 x 10.0
