Sphinkie/Radial-V/3D objects/Boitiers/Support for Amplifier.stl

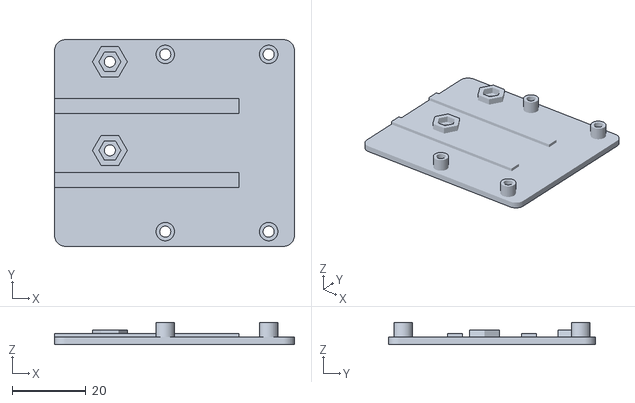
[picture p136: CAD file, 2024-02-11]
3D objects/Boitiers/Support for Amplifier.stl
65.0 x 56.0 x 6.00
