Sphinkie/Radial-V/3D objects/Support for Arduino Boards/files/Radial-V Angles (D).stl

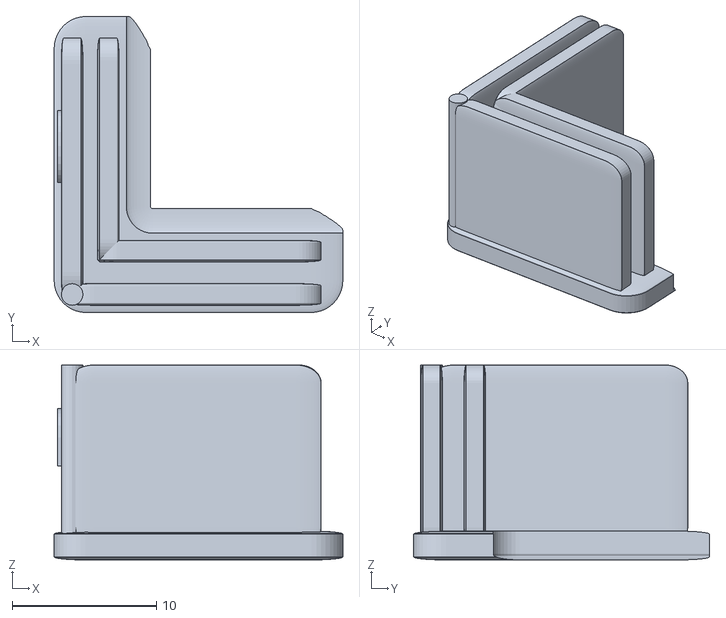
[picture p137: CAD file, 2020-01-11]
3D objects/Support for Arduino Boards/files/Radial-V Angles (D).stl
20.0 x 20.5 x 13.5
