Sphinkie/Radial-V/3D objects/Boitiers/Couvercle Adaptateur Audio.stl

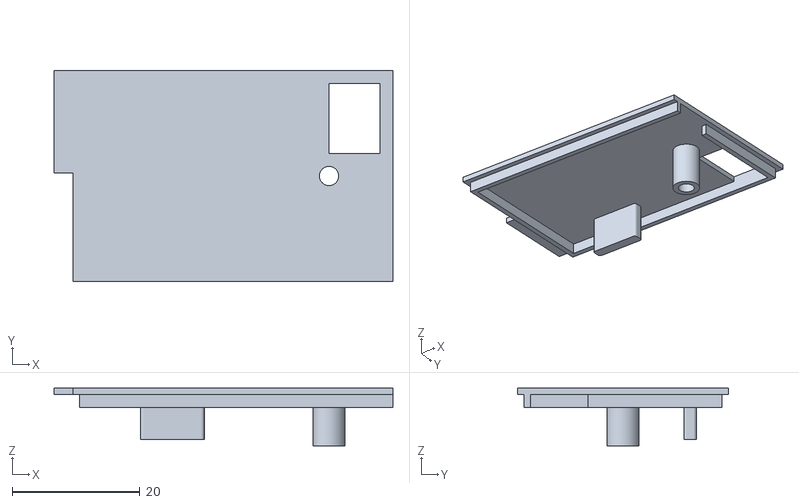
[picture p138: CAD file, 2024-02-11]
3D objects/Boitiers/Couvercle Adaptateur Audio.stl
53.0 x 33.0 x 9.00
