Sphinkie/Radial-V/3D objects/Boitiers/Couvercle_pour_Bus_Board.stl

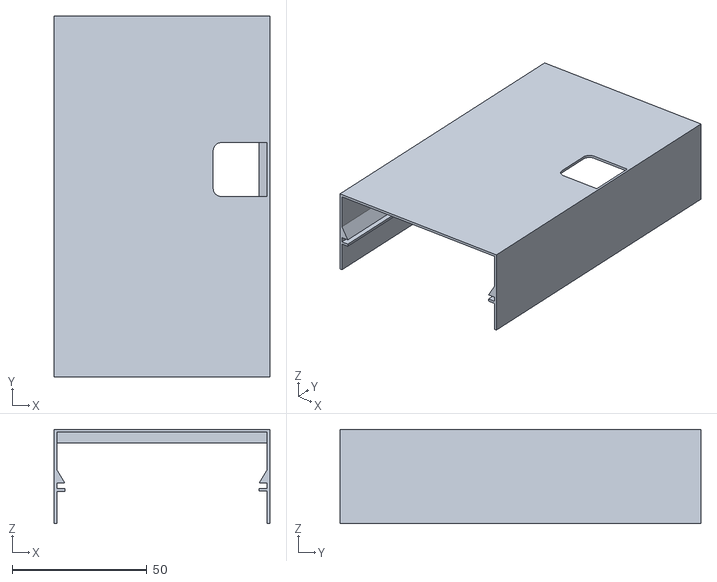
[picture p139: CAD file, 2024-02-11]
3D objects/Boitiers/Couvercle_pour_Bus_Board.stl
80.0 x 134.0 x 35.0
