Sphinkie/Radial-V/docs/images/Radial-V-tuning.png

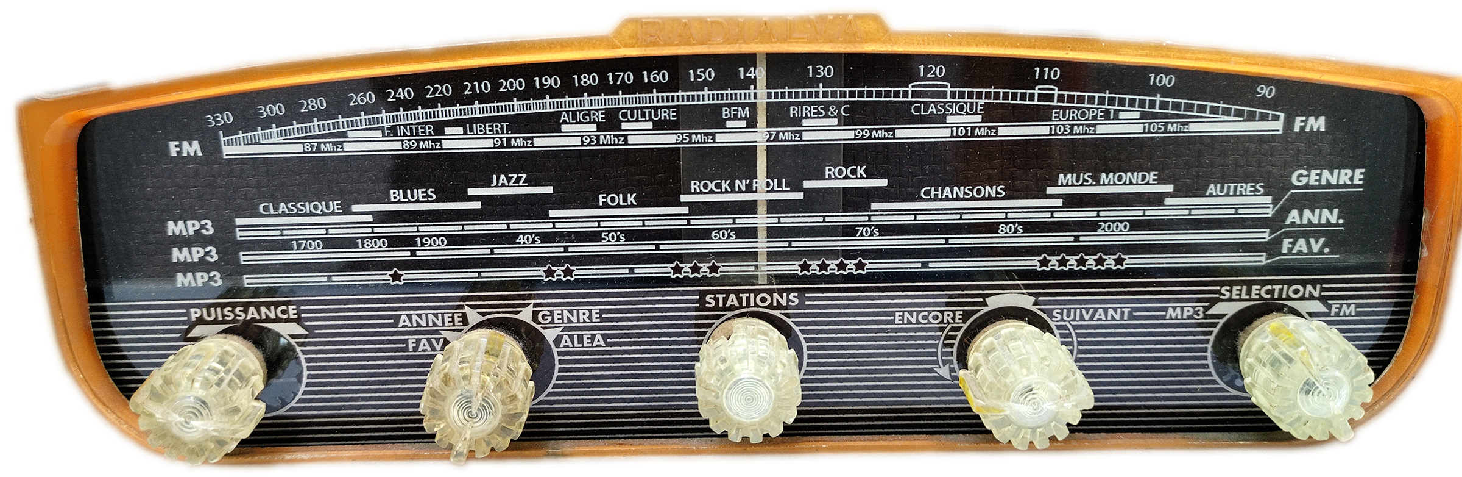
docs/images/Radial-V-tuning.png
