Sphinkie/Radial-V/External Hardware/Carte Sparkfun MP3 Player Shield/Documentation/MP3 Player Shield REV 1.3 Hookup - learn.sparkfun.pdf

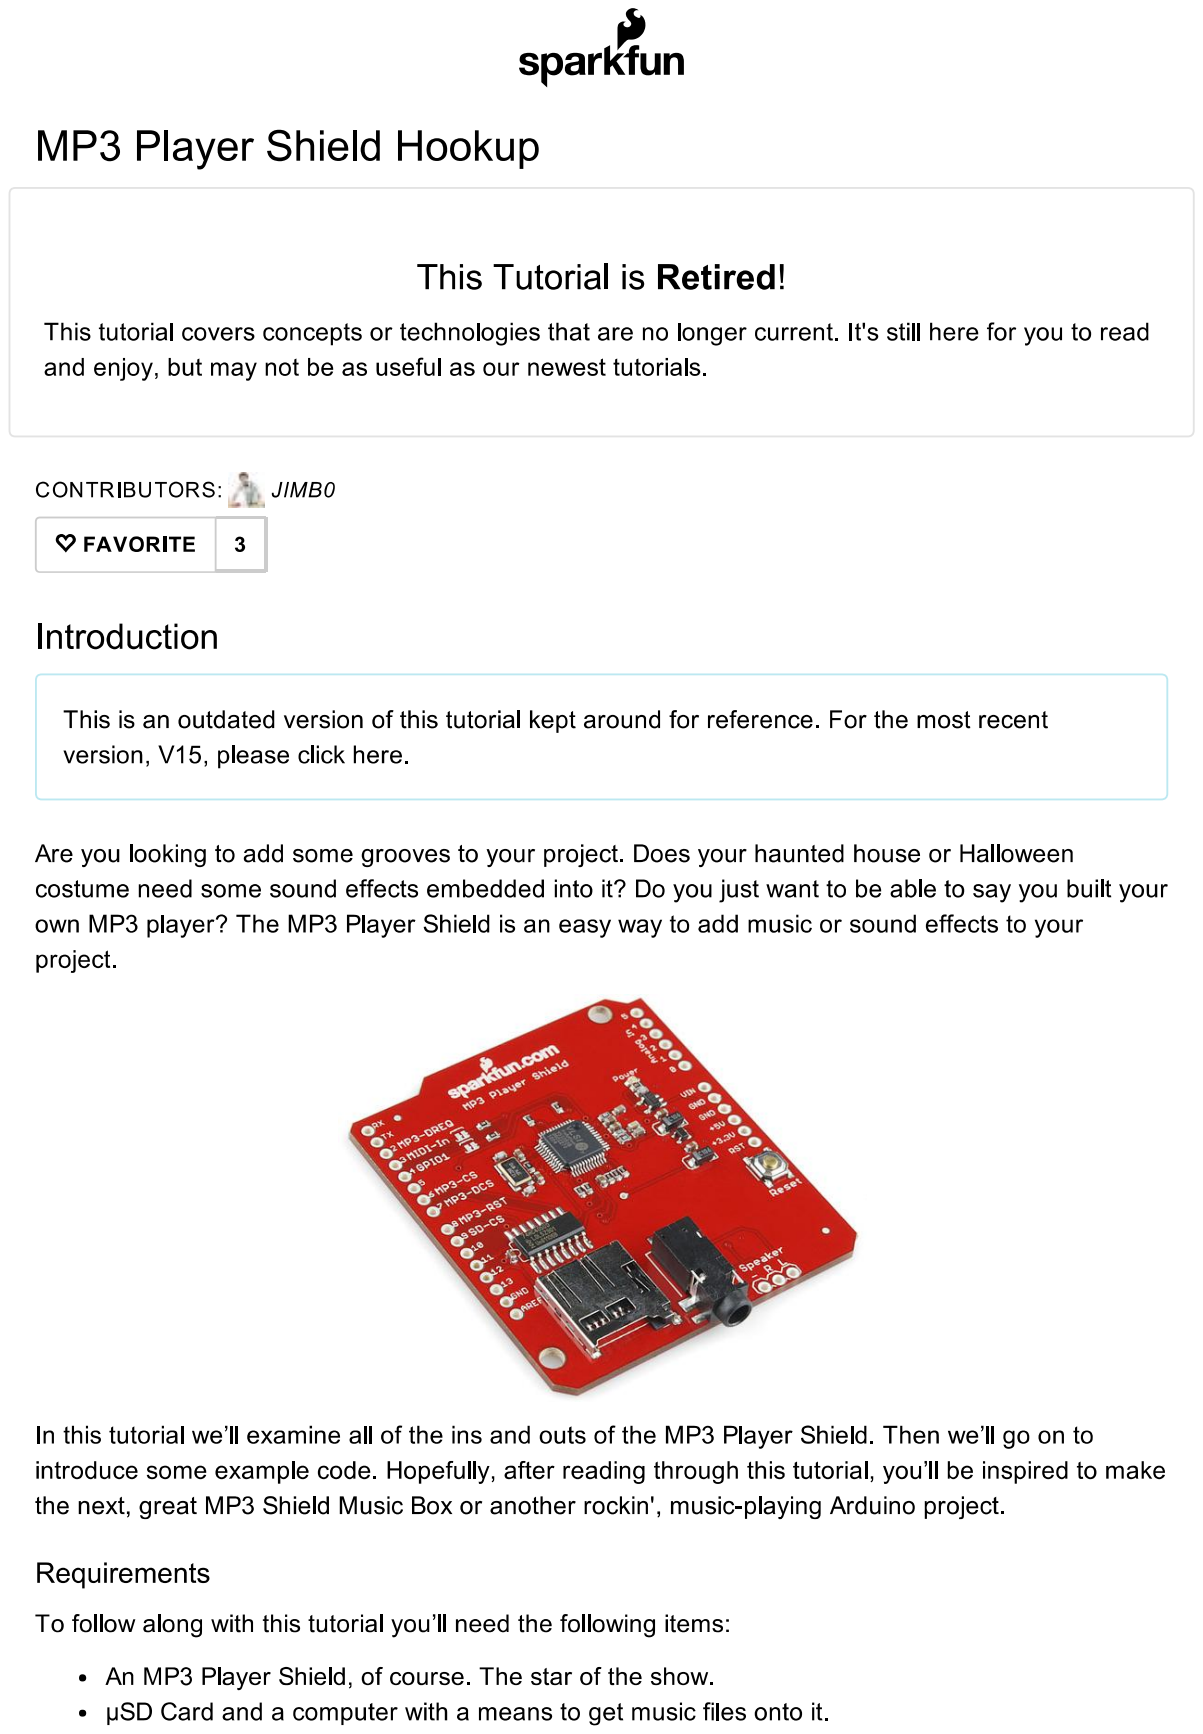
[picture p142: page 1]

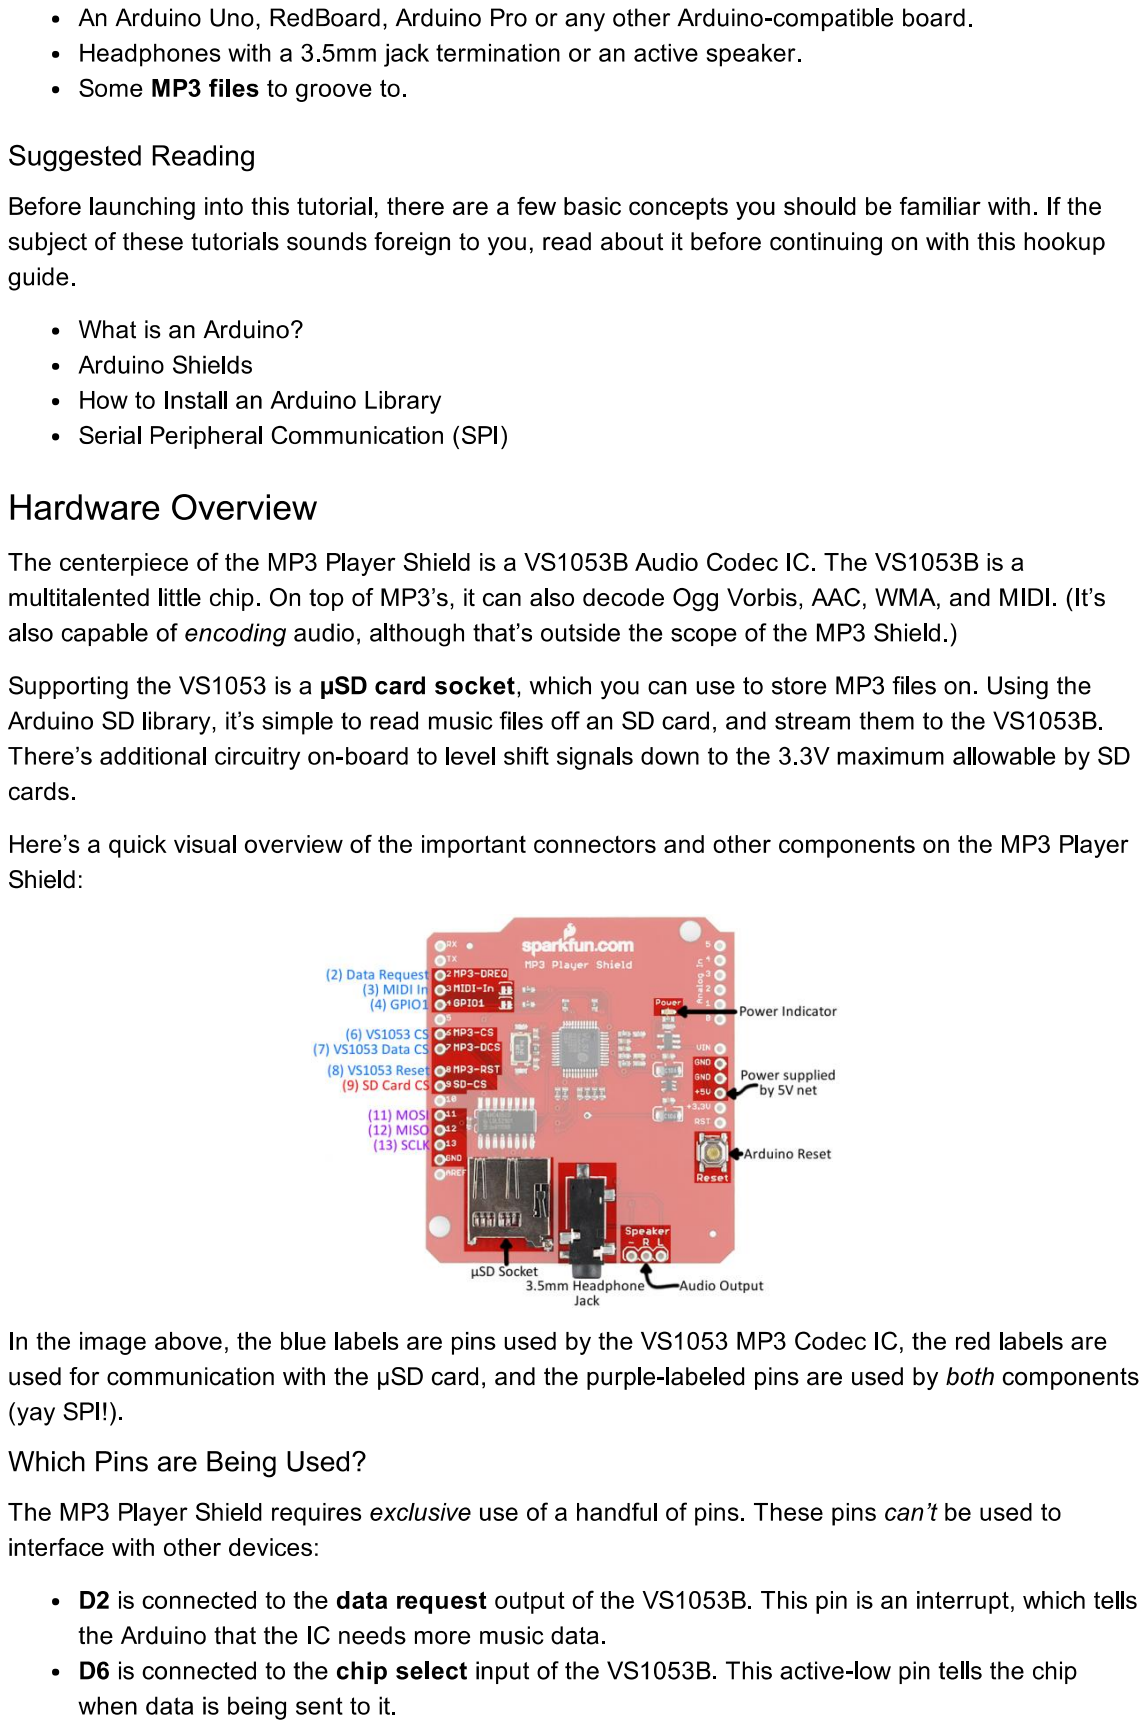
[picture p143: page 2]

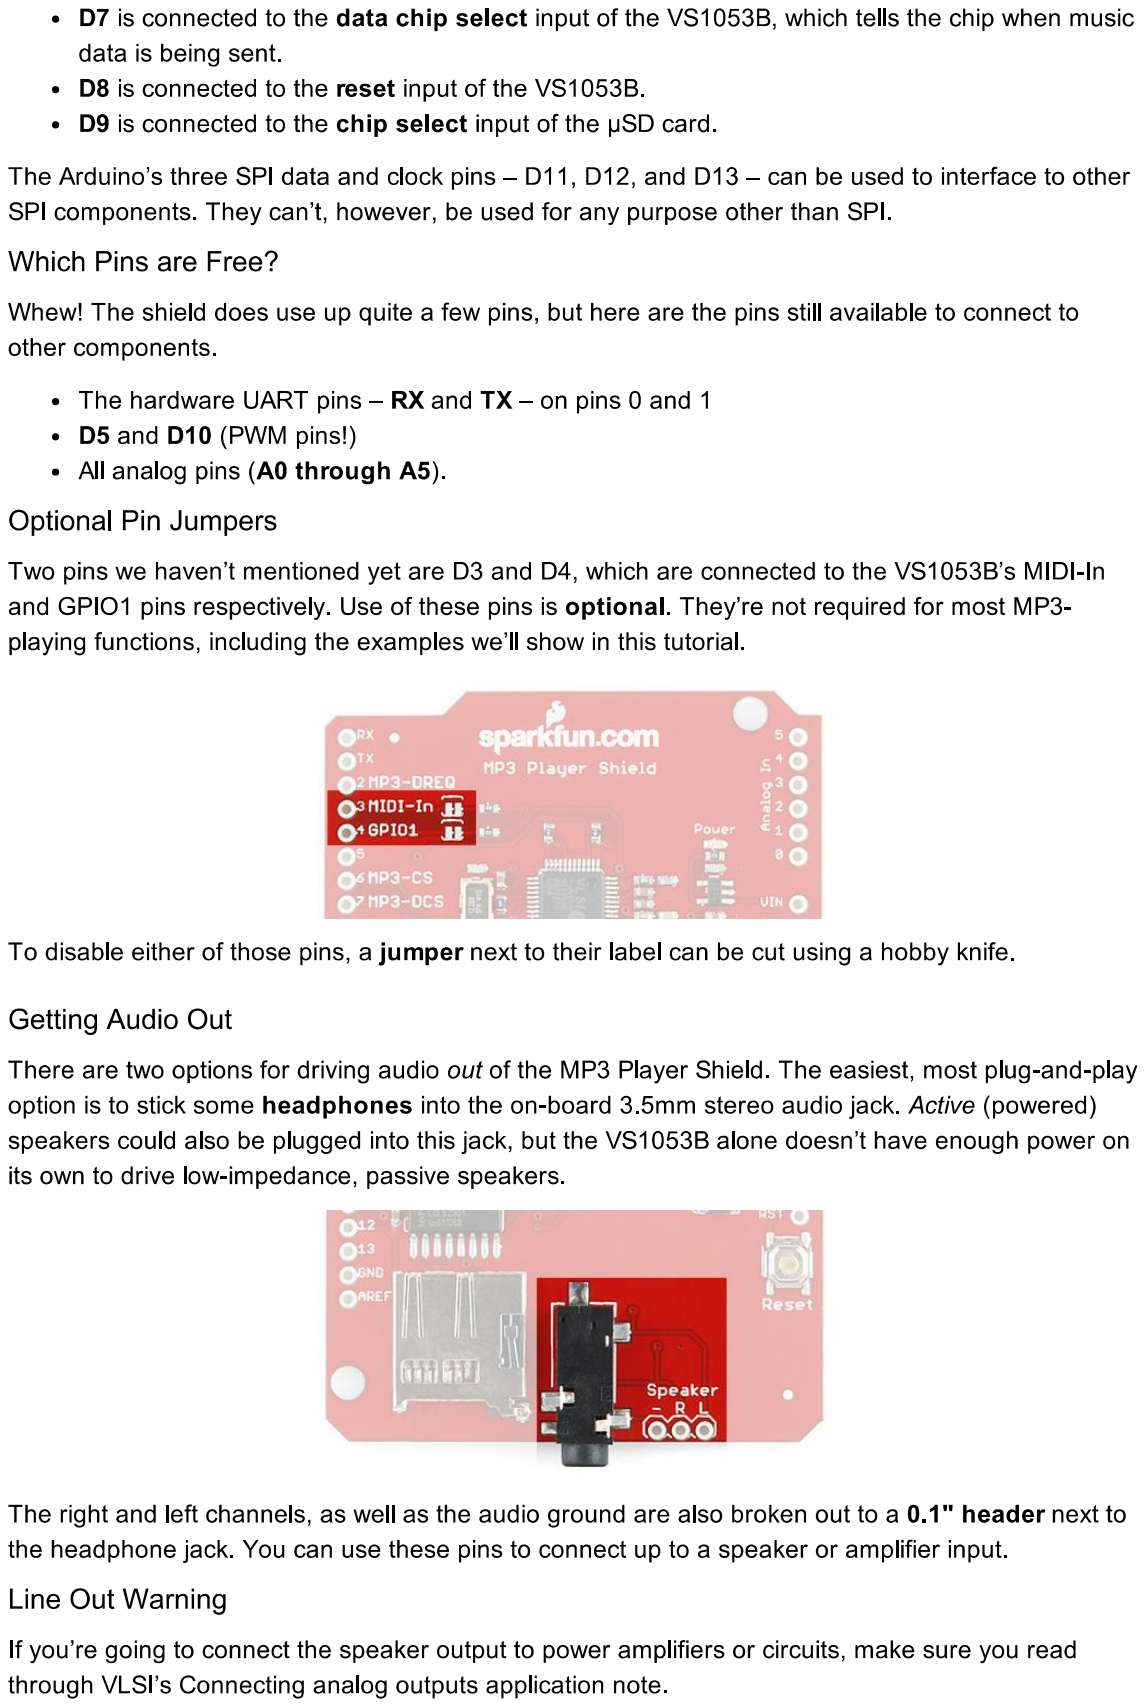
[picture p144: page 3]

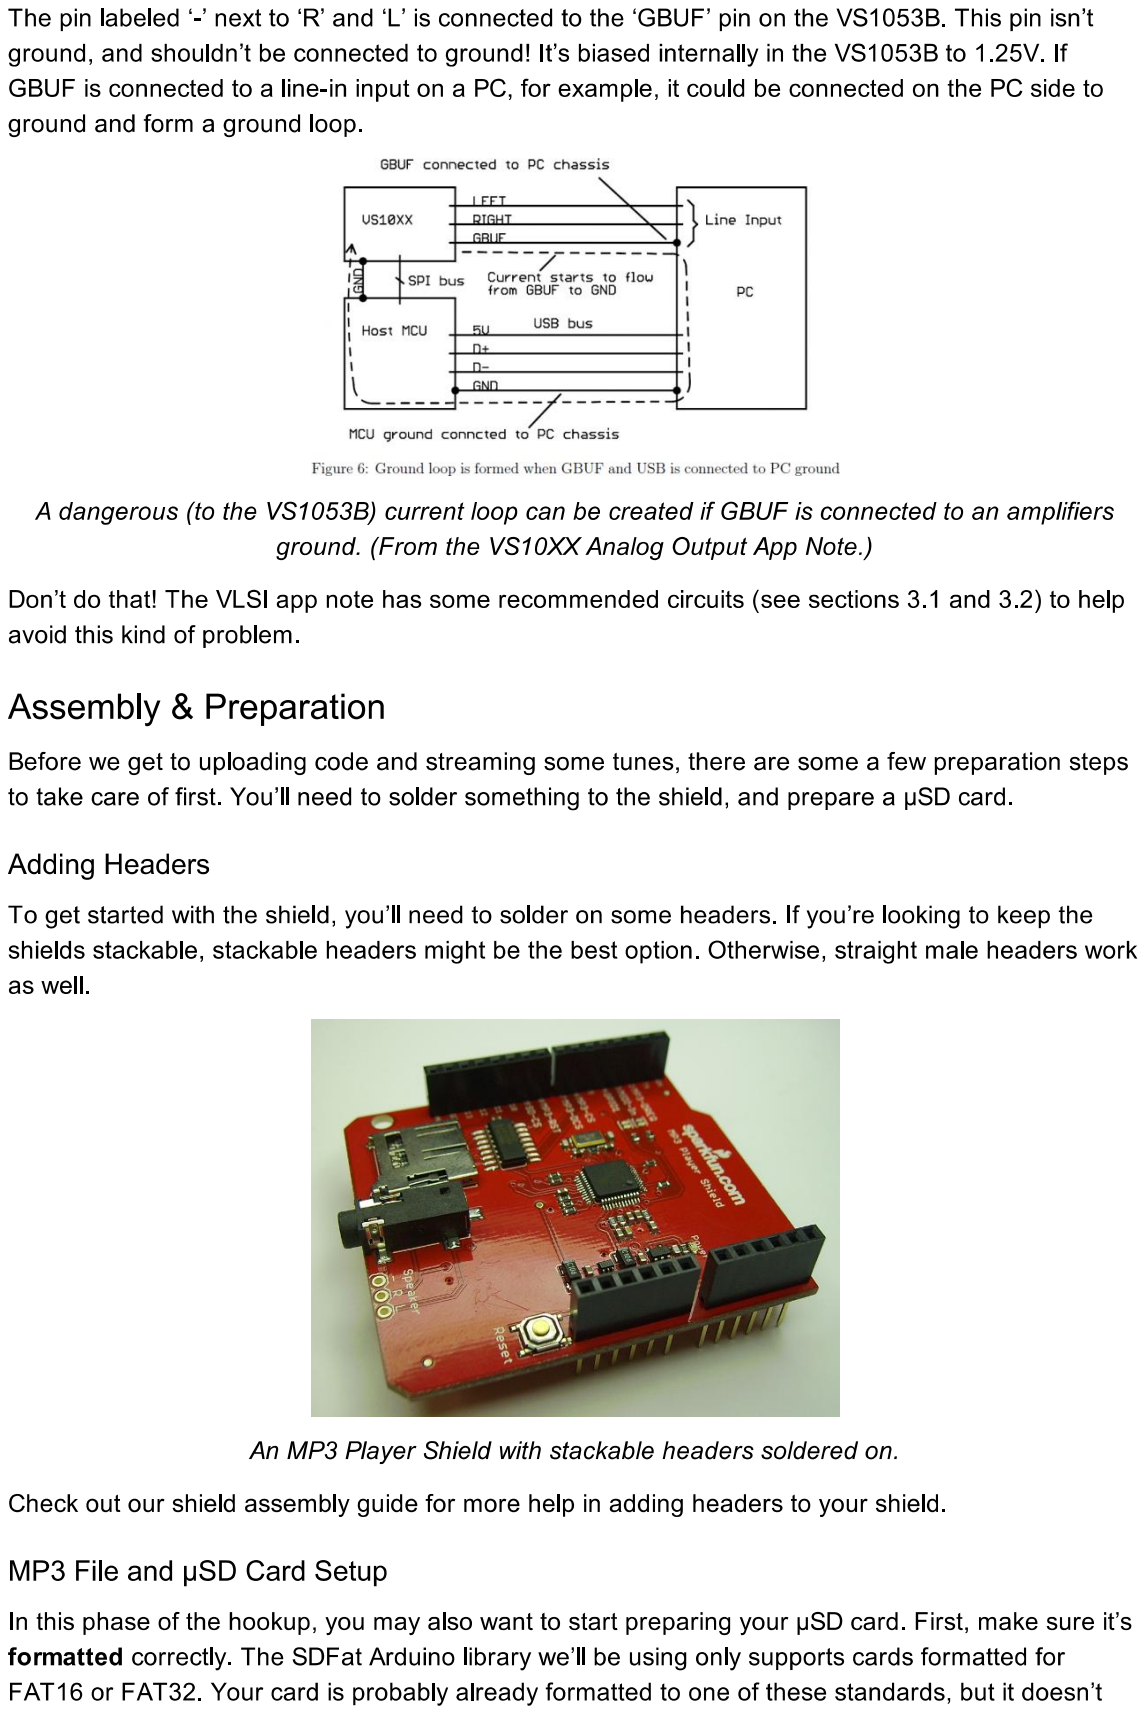
[picture p145: page 4]

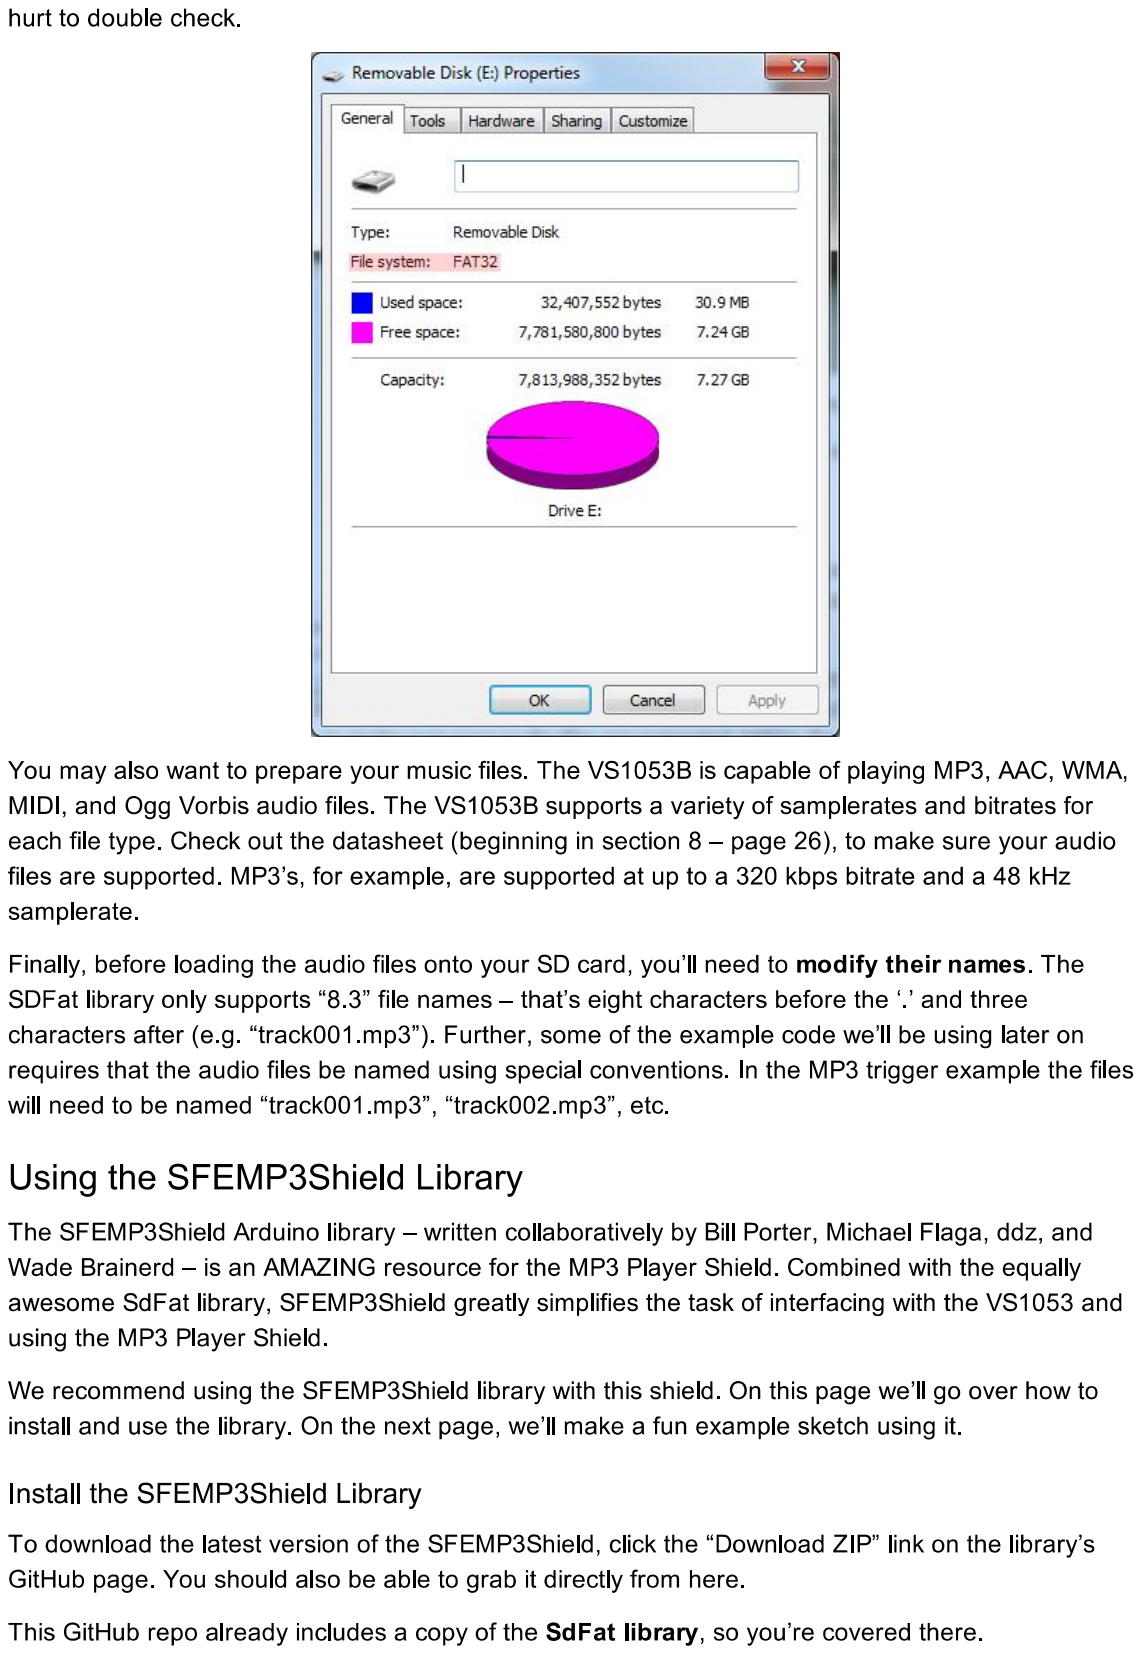
[picture p146: page 5]

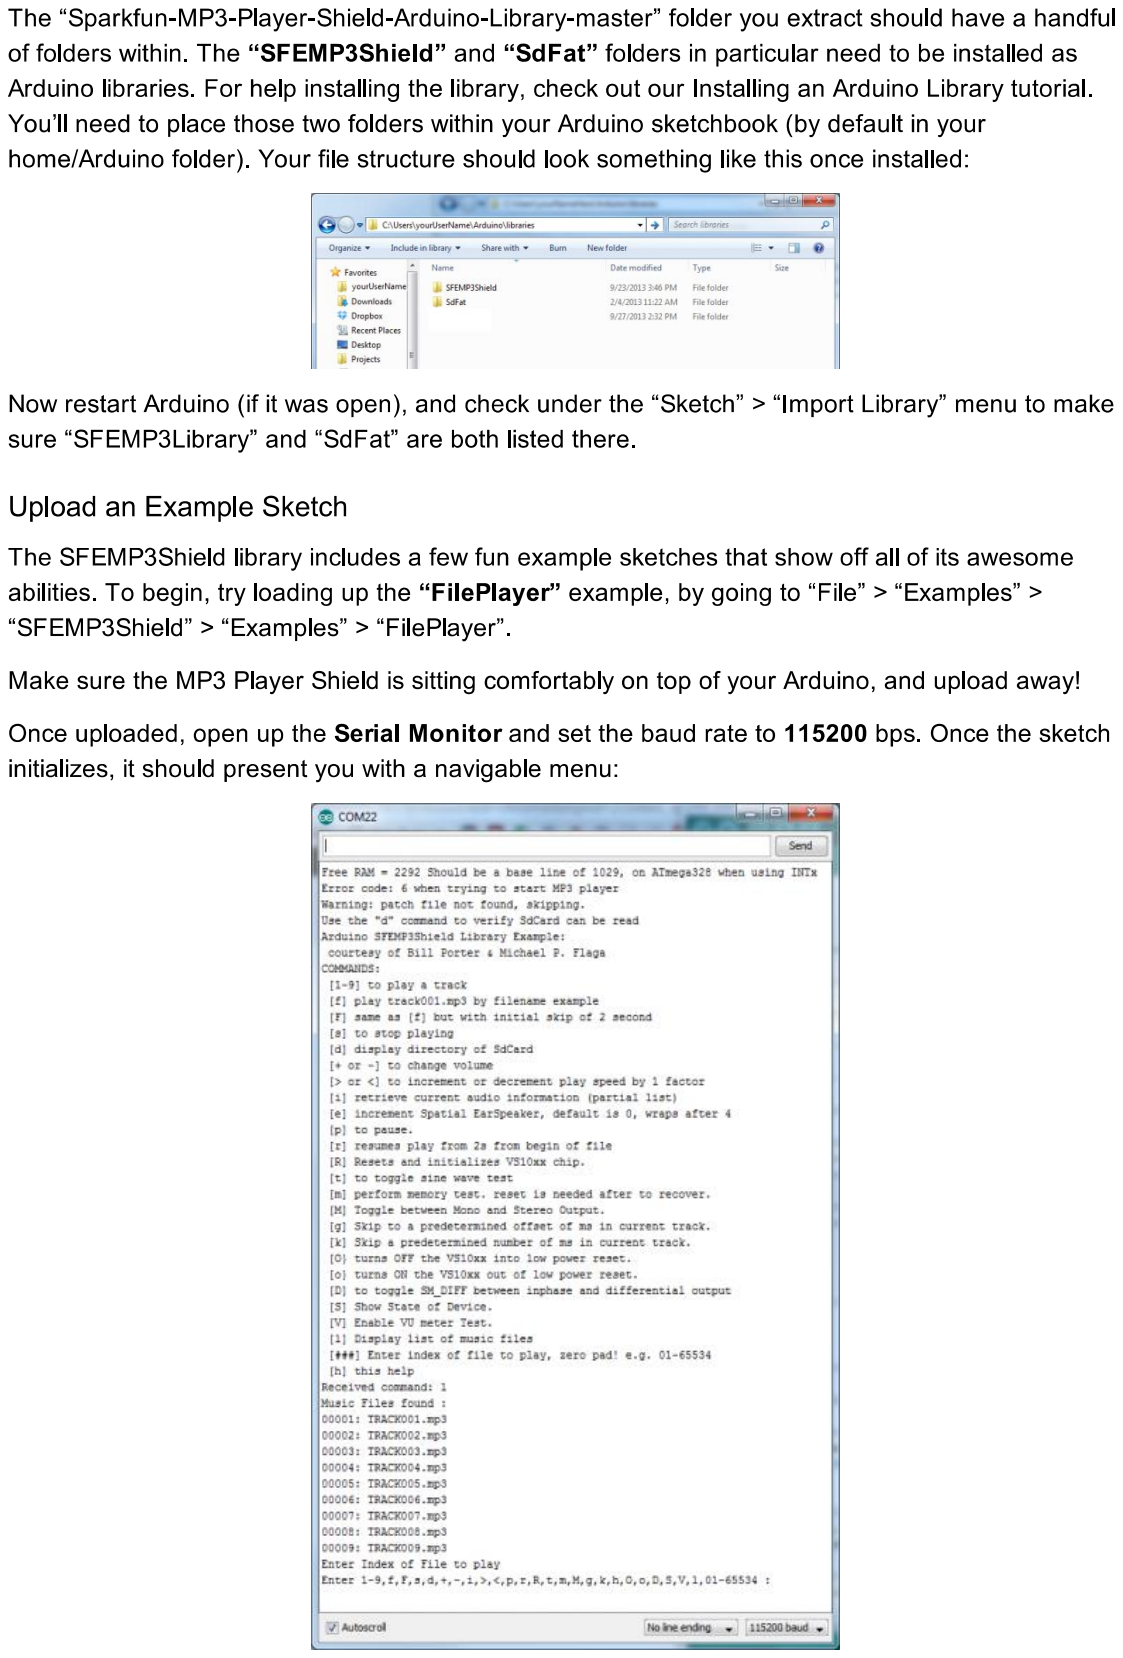
[picture p147: page 6]

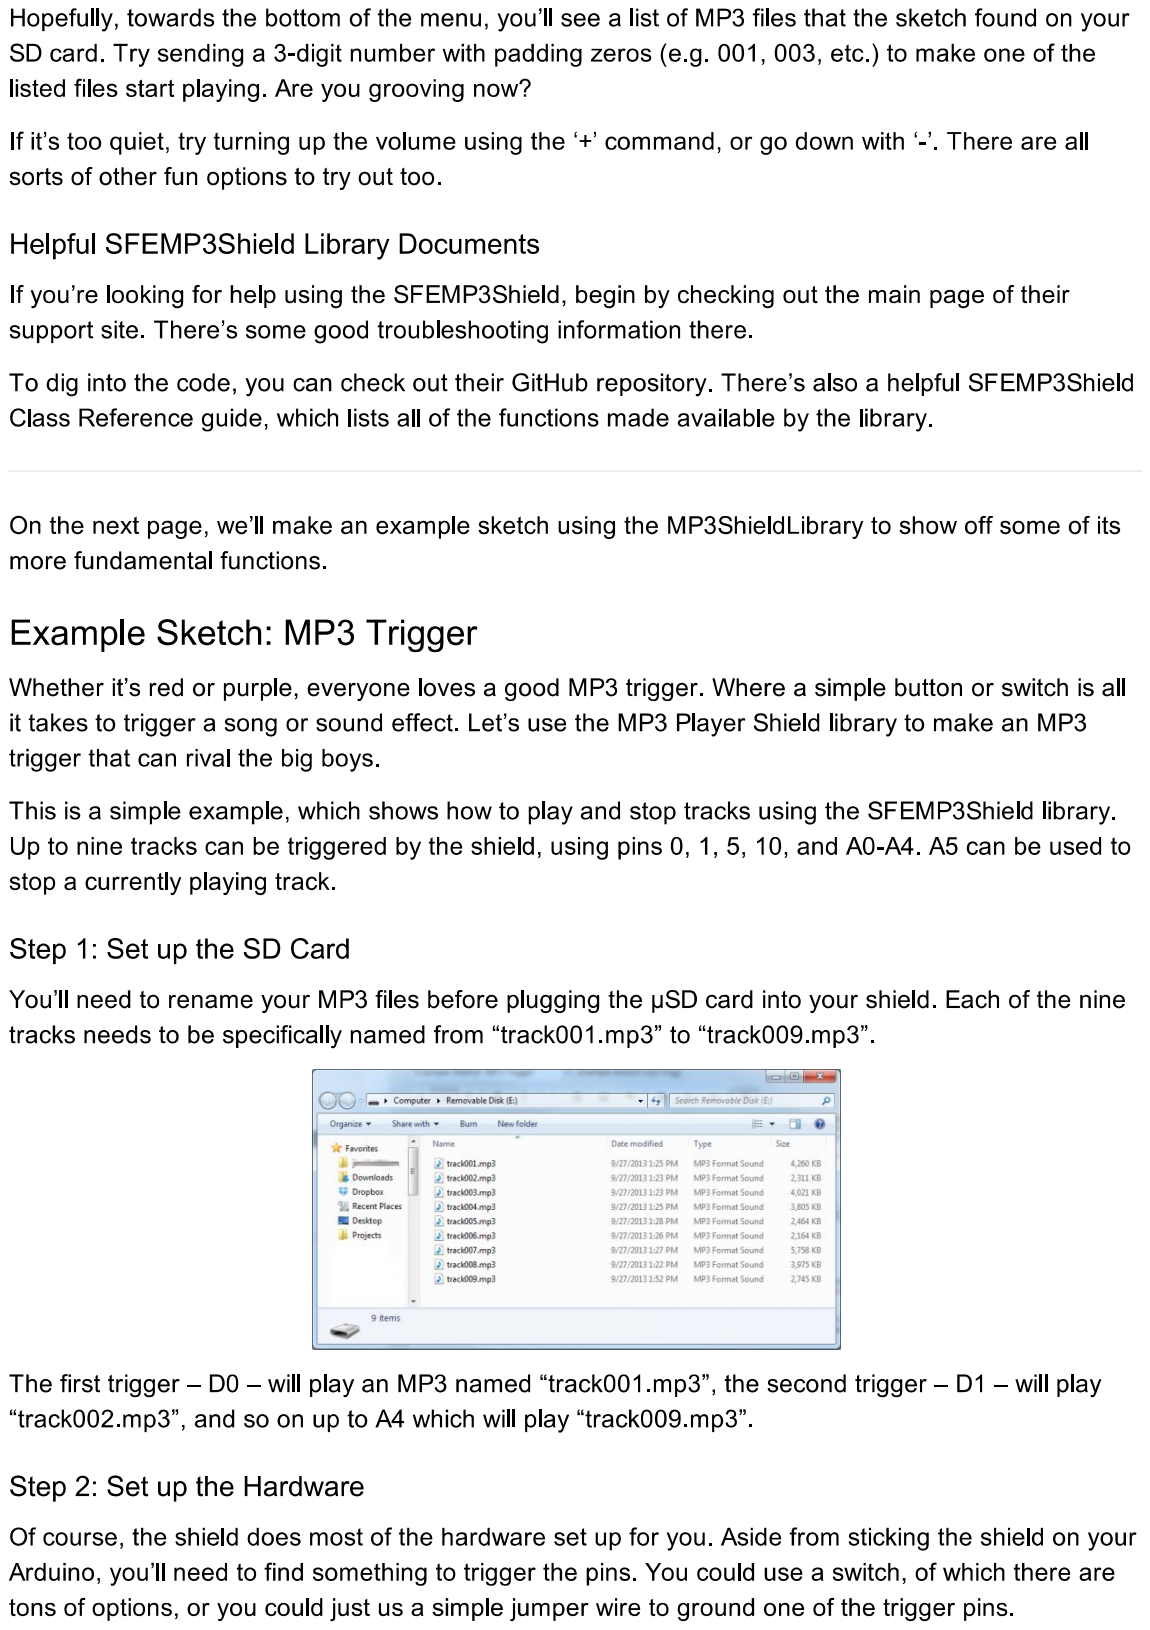
[picture p148: page 7]

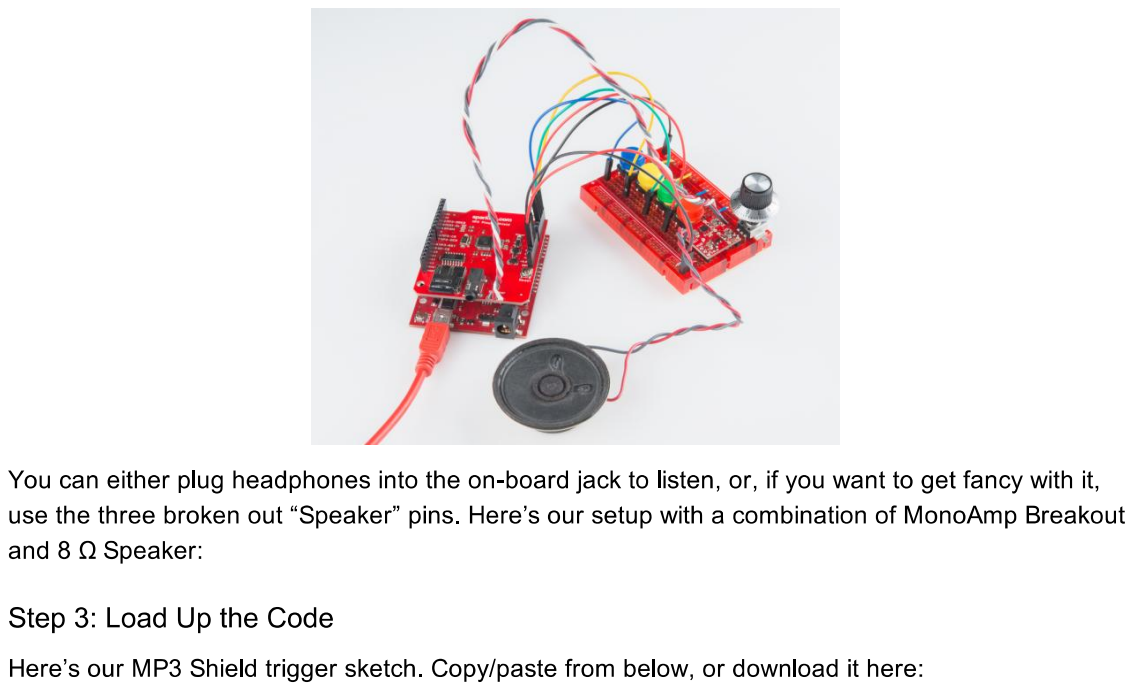
[picture p149: page 8]

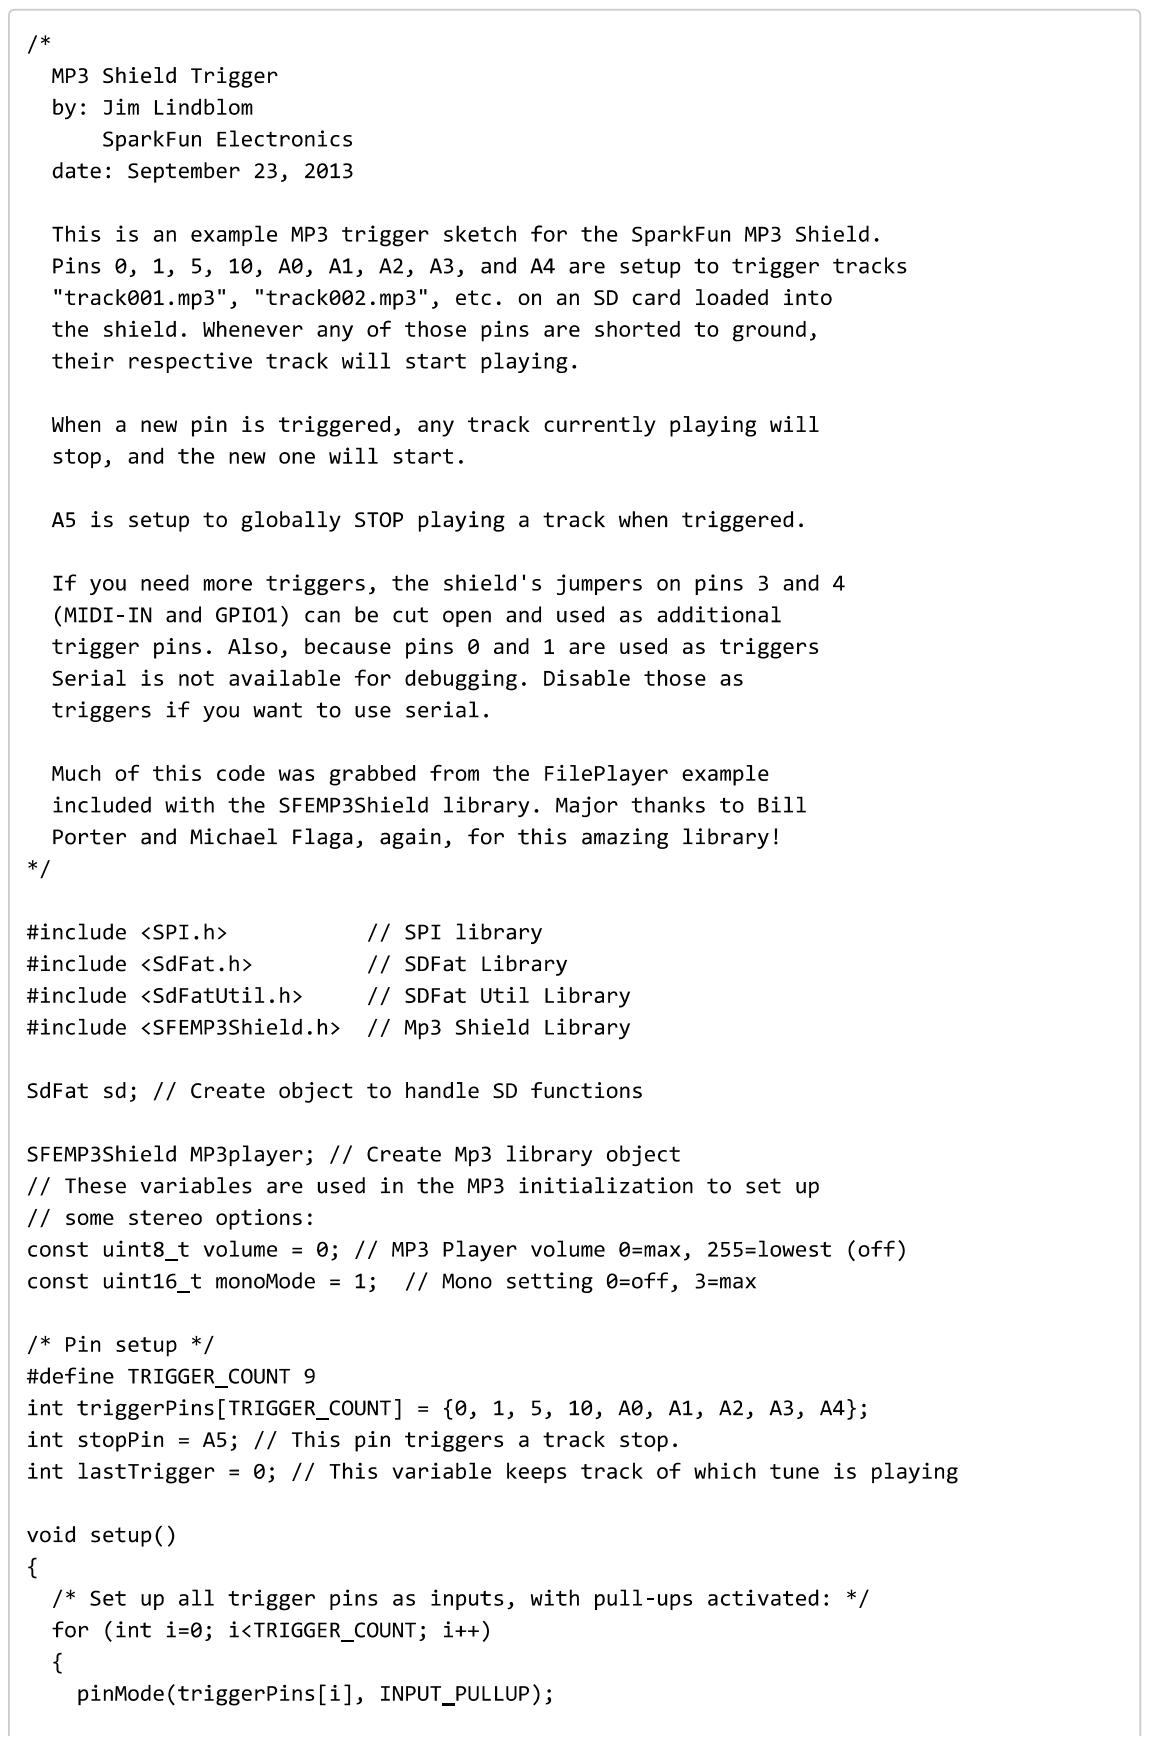
[picture p150: page 9]

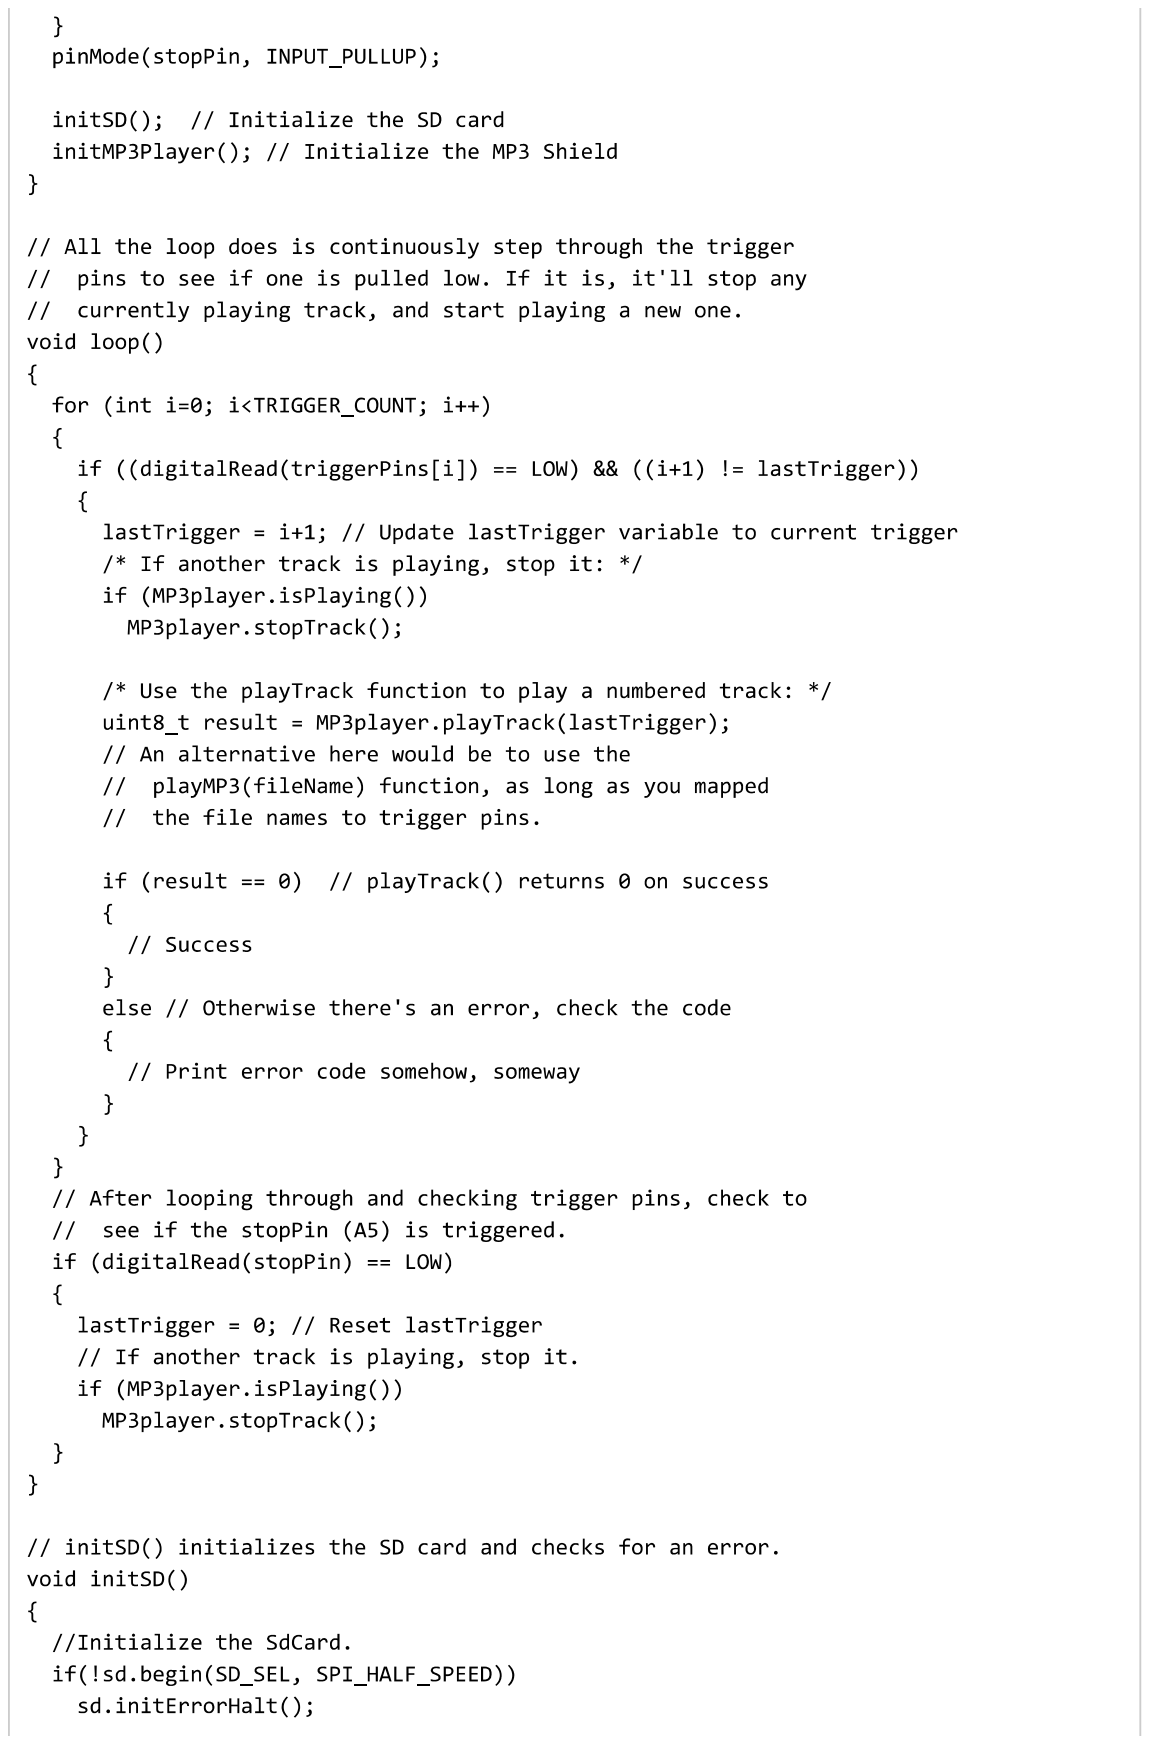
[picture p151: page 10]

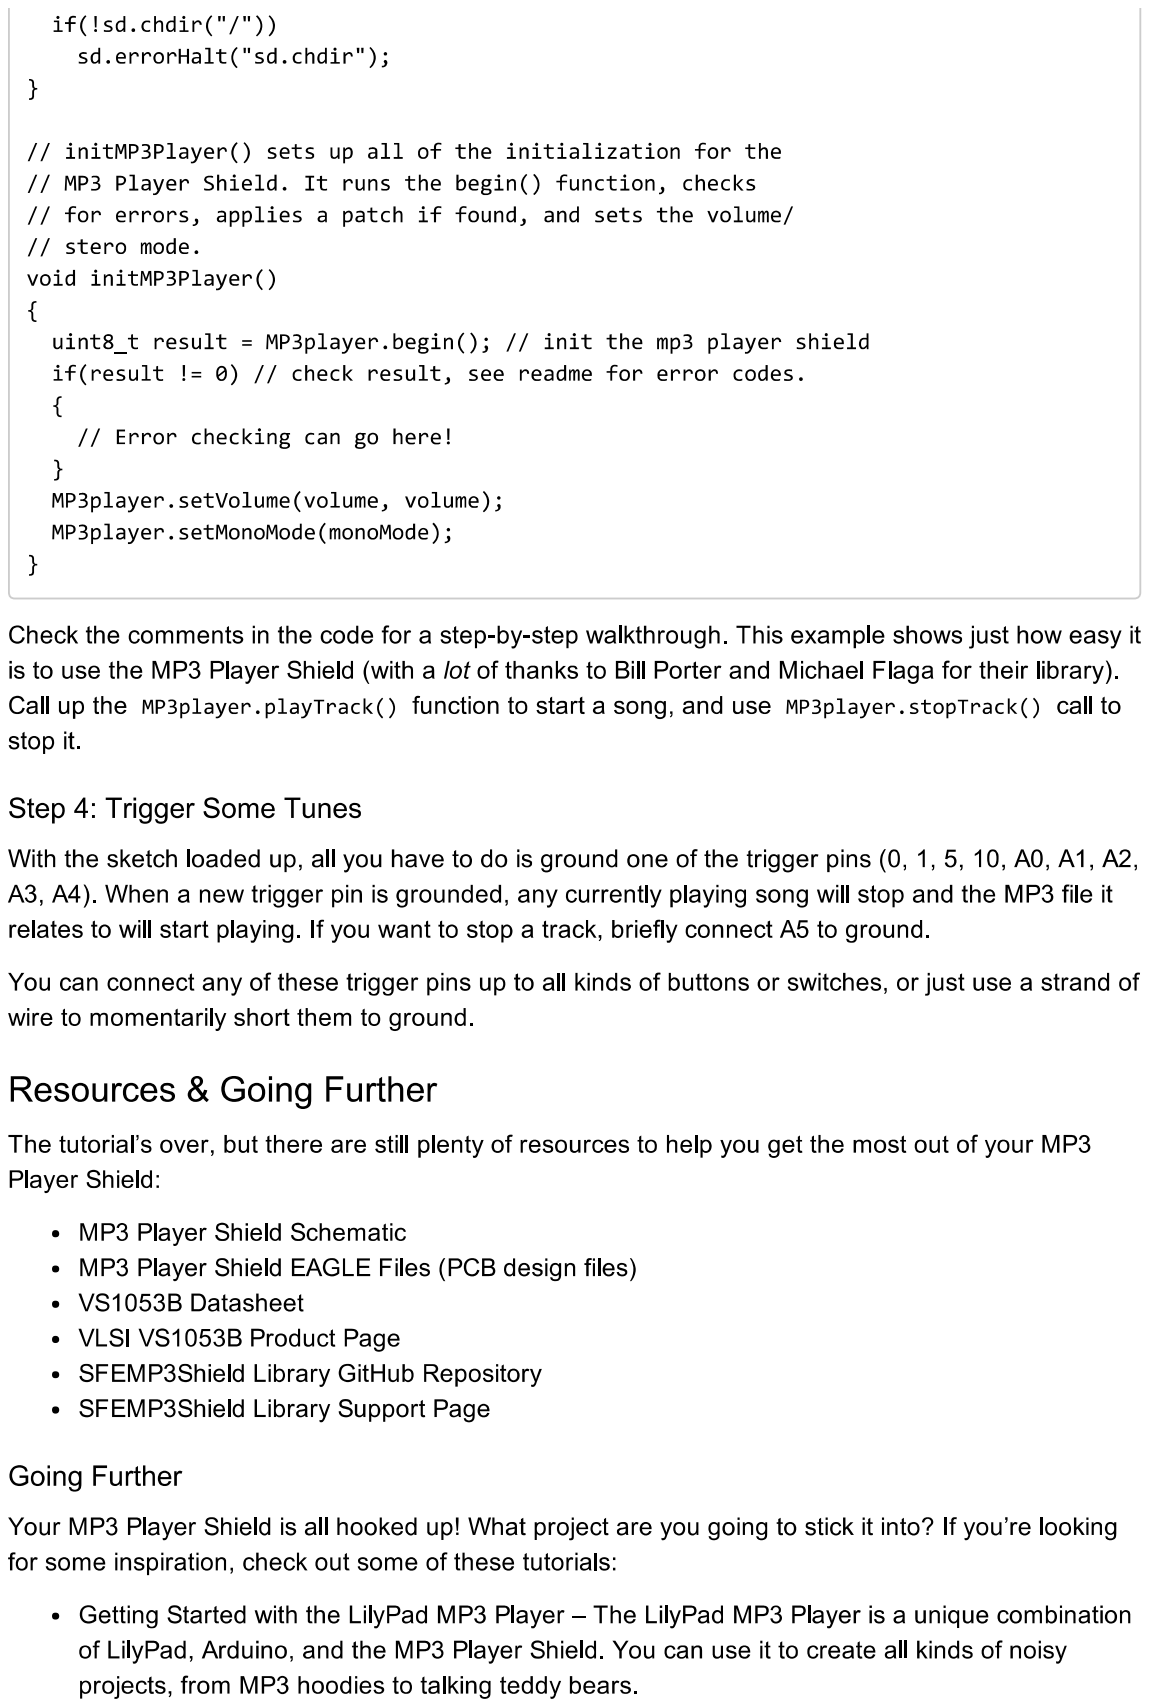
[picture p152: page 11]
