Sphinkie/Radial-V/External Hardware/Carte Sparkfun MP3 Player Shield/Documentation/MP3 Shield-v13.pdf

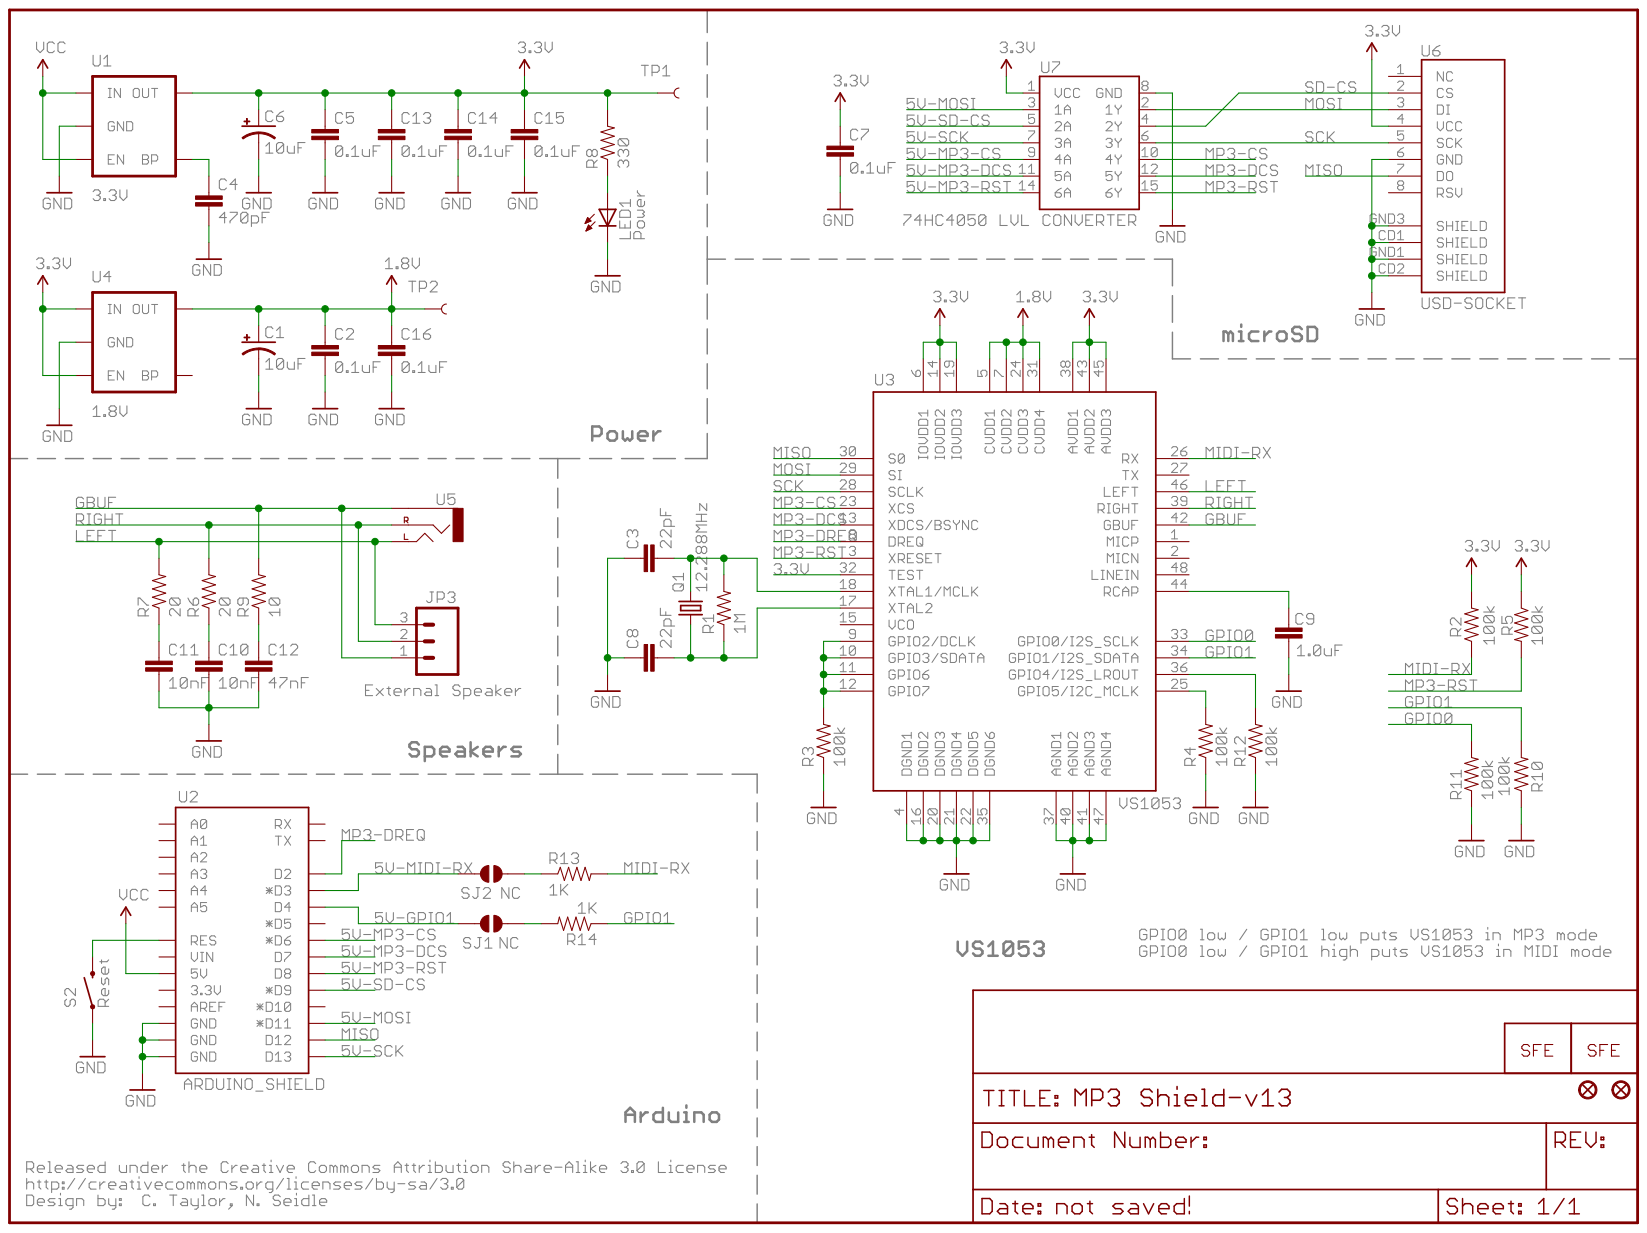
[picture p153: page 1]
