Sphinkie/Radial-V/External Hardware/Carte Sparkfun MP3 Player Shield/Documentation/SparkFun MP3 Player Shield - DEV-10628 - SparkFun Electronics.pdf

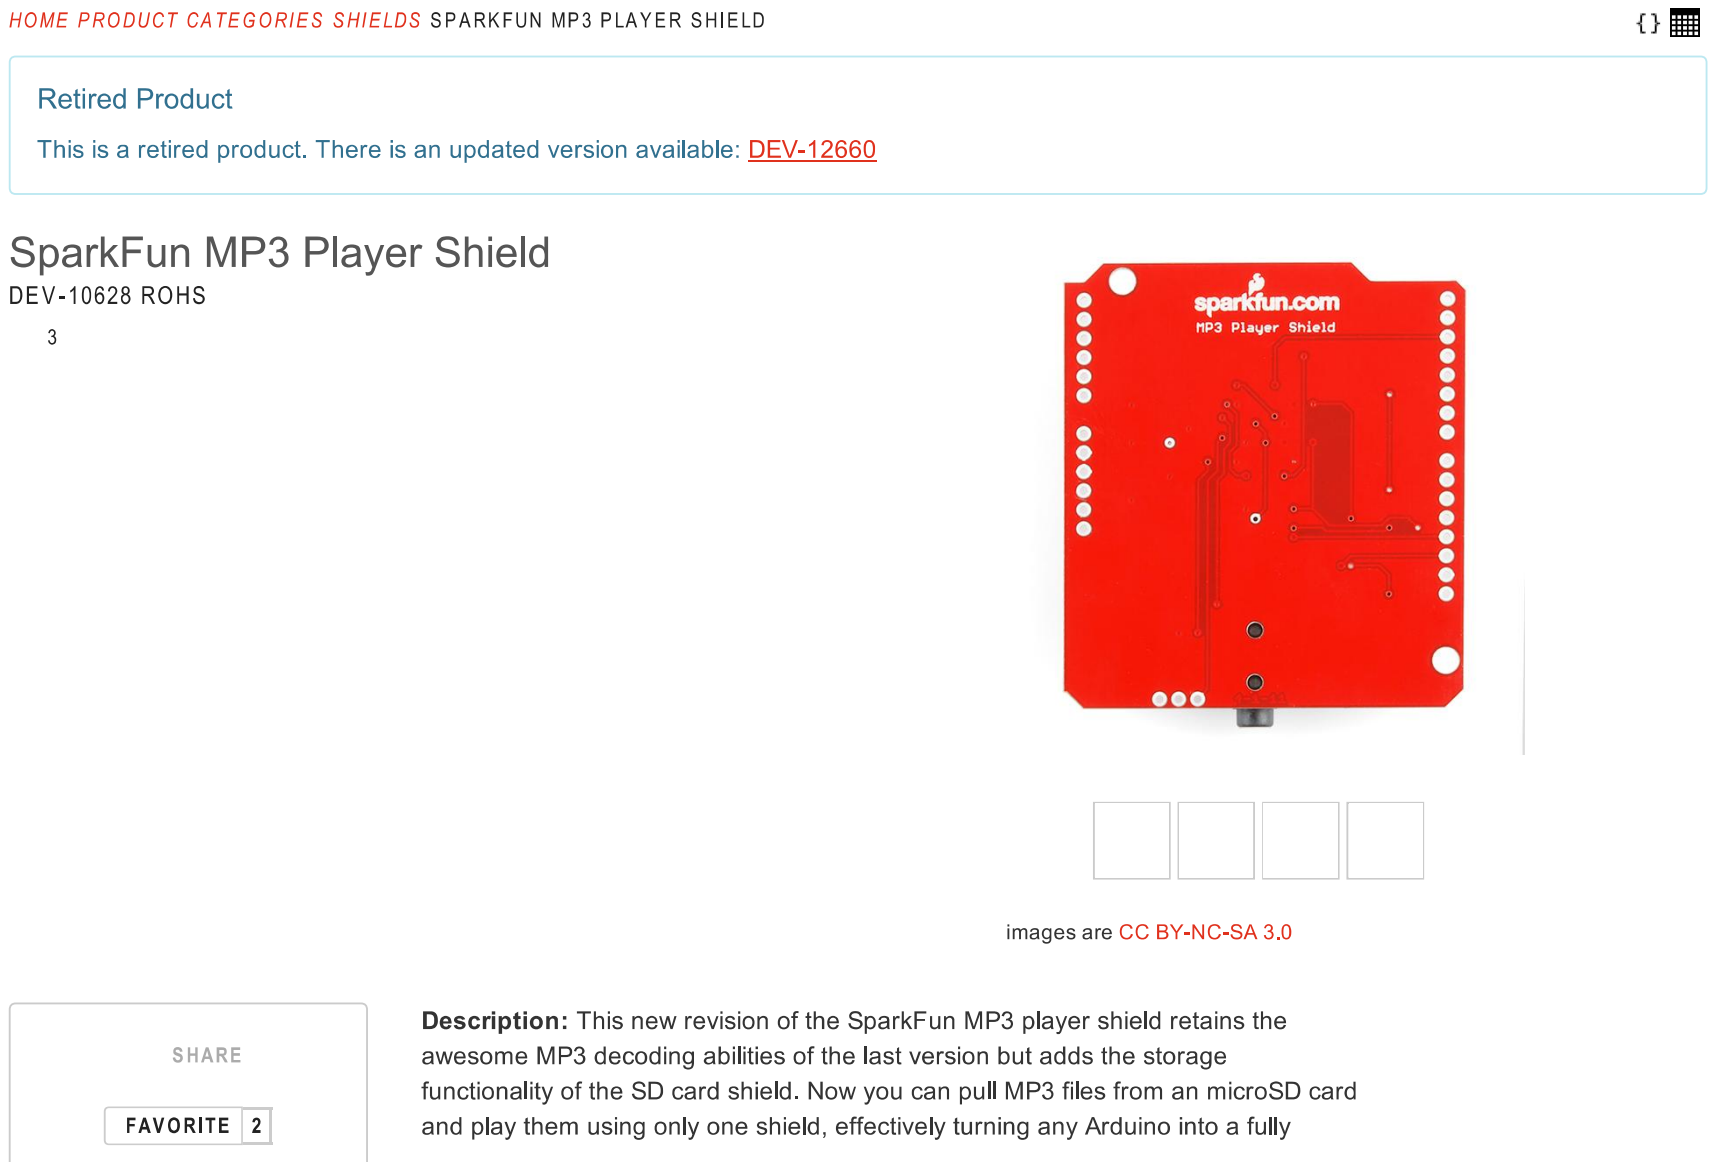
[picture p154: page 1]

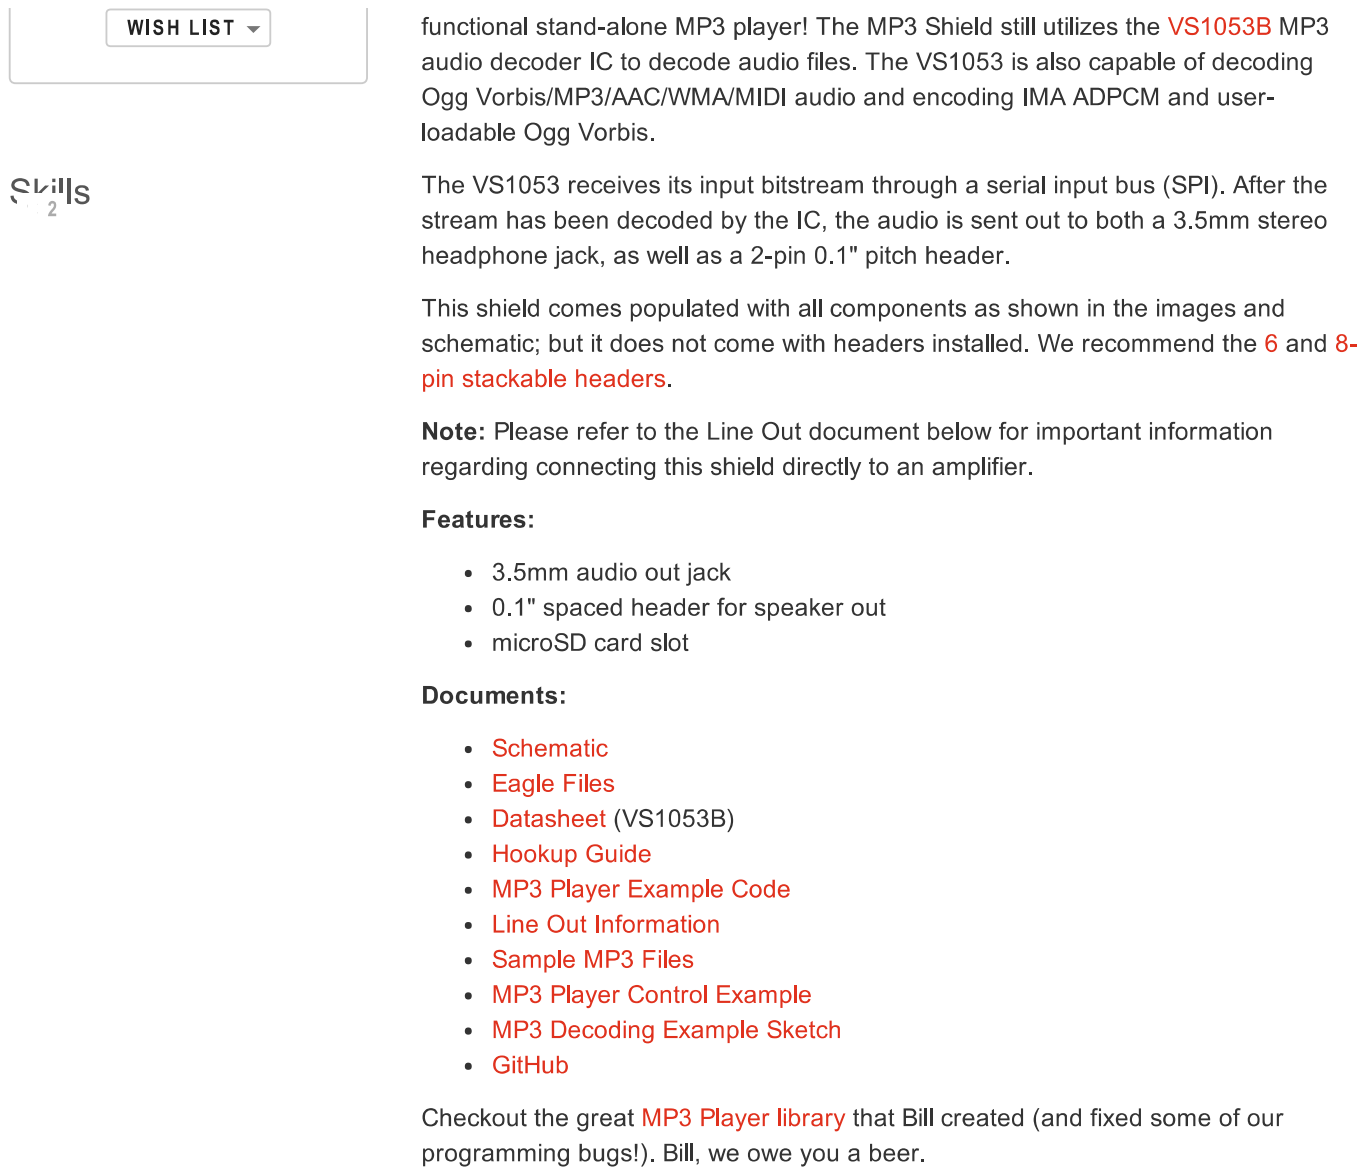
[picture p155: page 2]
