Sphinkie/Radial-V/schematics/Radial-V extension board/Radial-V Ext.sch

## EAGLE design schematics/Radial-V extension board/Radial-V Ext.sch (2018-01-25)

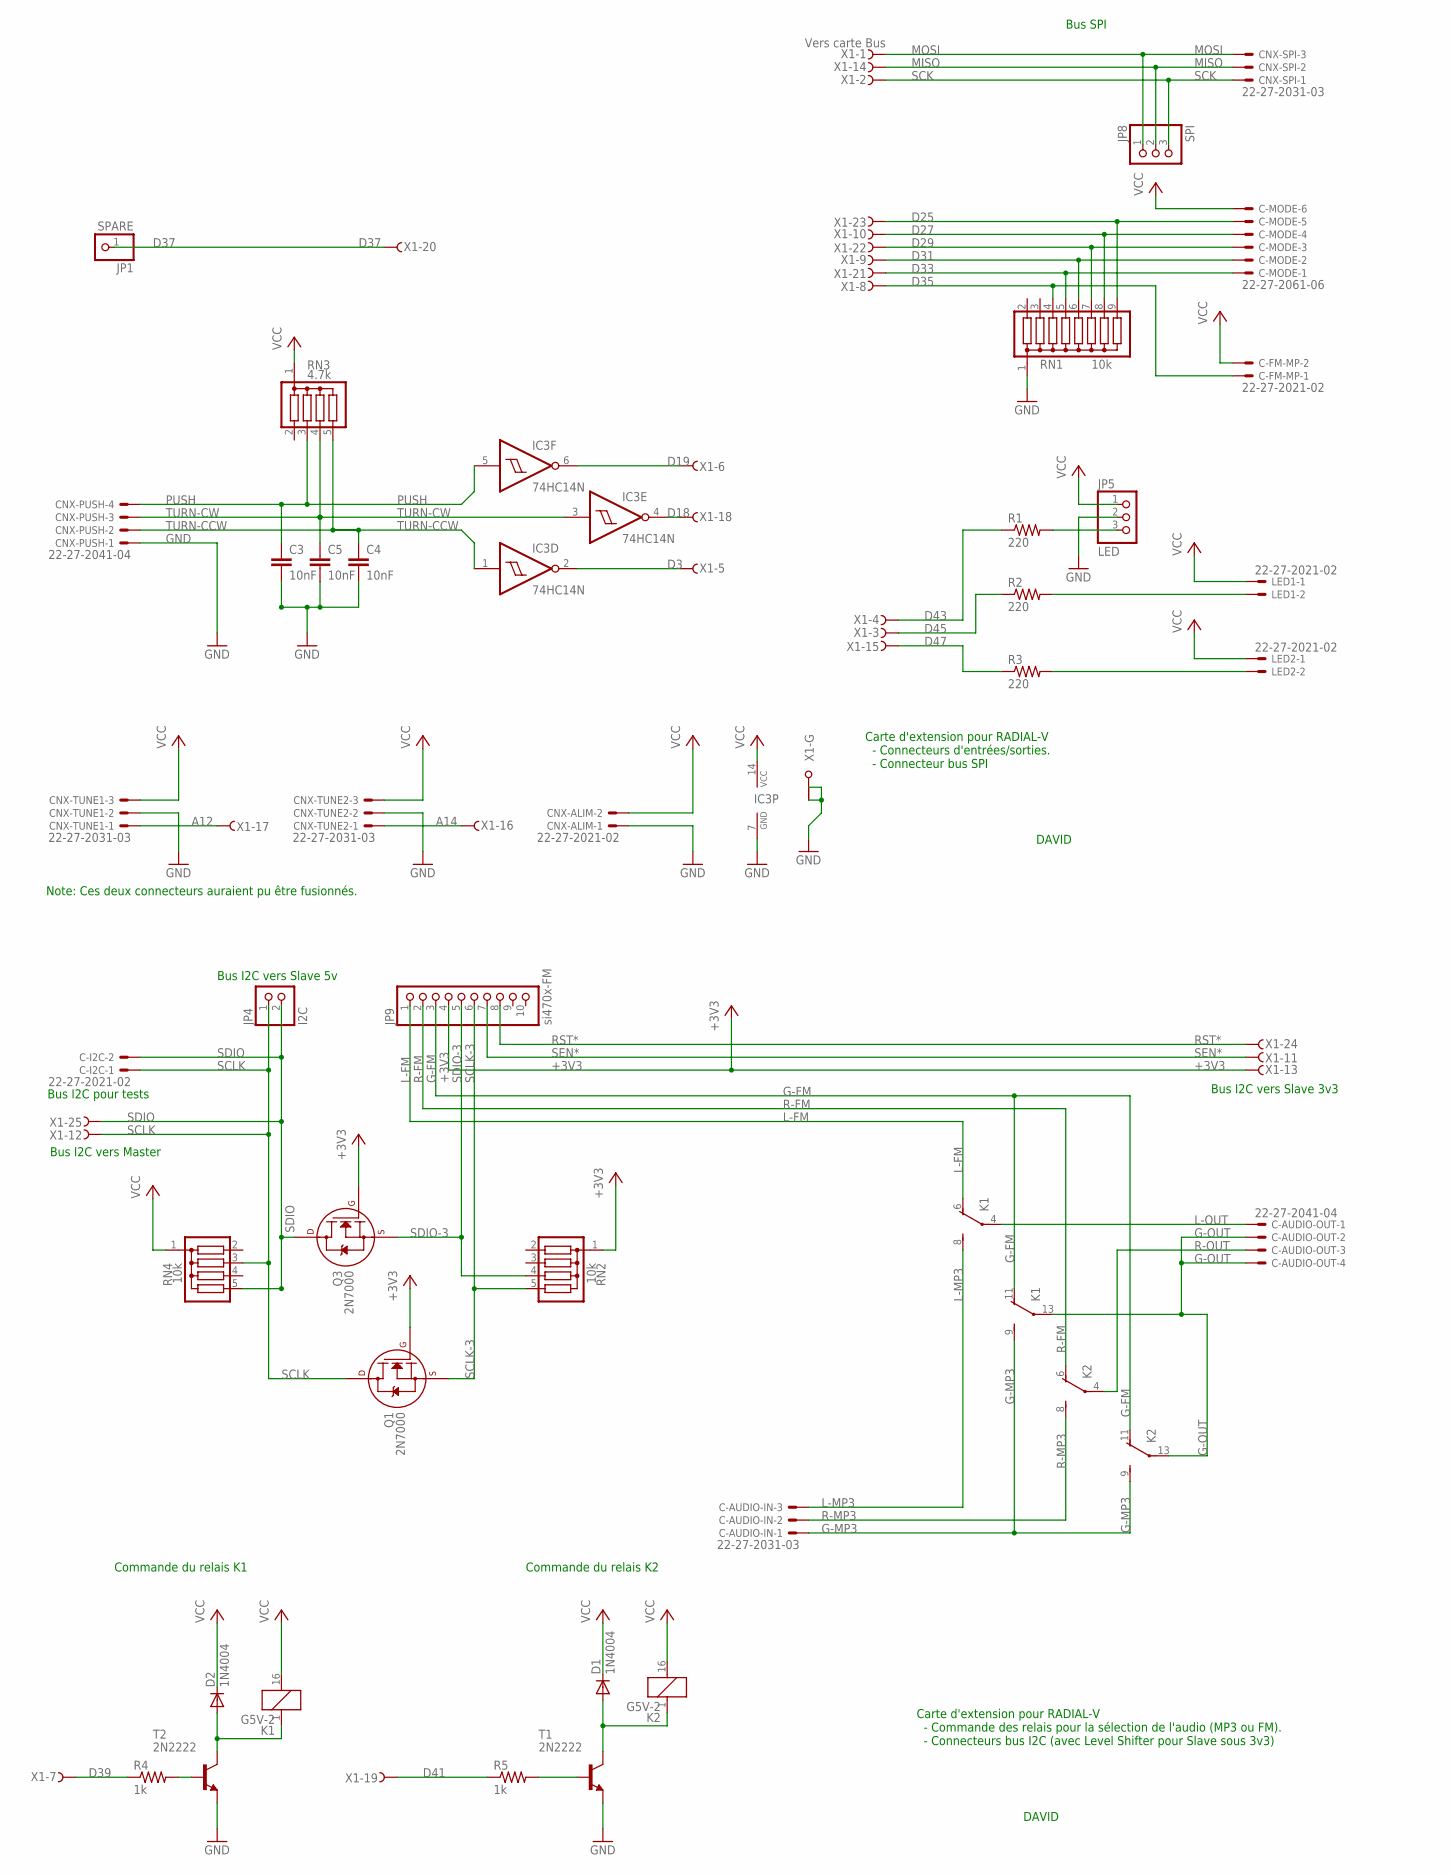
[picture p175: schematic Radial-V Ext.sch]

Parts:
C3, C4, C5: 10nF; C050-050X075
C-AUDIO-IN: 22-27-2031-03; 6410-03
C-AUDIO-OUT: 22-27-2041-04; 6410-04
C-FM-MP: 22-27-2021-02; 6410-02
C-I2C: 22-27-2021-02; 6410-02
C-MODE: 22-27-2061-06; 6410-06
CNX-ALIM: 22-27-2021-02; 6410-02
CNX-PUSH: 22-27-2041-04; 6410-04
CNX-SPI: 22-27-2031-03; 6410-03
CNX-TUNE1, CNX-TUNE2: 22-27-2031-03; 6410-03
D1, D2: 1N4004; DO41-10
IC3: 74HC14N; DIL14
JP1: SPARE; 1X01
JP4: I2C; 1X02
JP5: LED; 1X03
JP8: SPI; 1X03
JP9: si470x-FM; 1X10
K1, K2: G5V-2
LED1, LED2: 22-27-2021-02; 6410-02
Q1, Q3: 2N7000; TO-92
R1, R2, R3: 220; 0411/15
R4, R5: 1k; 0411/15
RN1: 10k; SIL9
RN2, RN4: 10k; SIL5
RN3: 4.7k; SIL5
T1, T2: 2N2222; TO18
X1: Vers carte Bus; F25HP

Connections:
+3V3: JP9.4, Q1.2 (G), Q3.2 (G), RN2.1, X1.13 (F)
A12: CNX-TUNE1.1, X1.17 (F)
A14: CNX-TUNE2.1, X1.16 (F)
D3: IC3.2 (O), X1.5 (F)
D18: IC3.4 (O), X1.18 (F)
D19: IC3.6 (O), X1.6 (F)
D25: C-MODE.5, RN1.9, X1.23 (F)
D27: C-MODE.4, RN1.8, X1.10 (F)
D29: C-MODE.3, RN1.7, X1.22 (F)
D31: C-MODE.2, RN1.6, X1.9 (F)
D33: C-MODE.1, RN1.5, X1.21 (F)
D35: C-FM-MP.1, RN1.4, X1.8 (F)
D37: JP1.1, X1.20 (F)
D39: R4.1, X1.7 (F)
D41: R5.1, X1.19 (F)
D43: R1.1, X1.4 (F)
D45: R2.1, X1.3 (F)
D47: R3.1, X1.15 (F)
G-FM: JP9.3, K1.11 (O), K2.11 (O)
G-MP3: C-AUDIO-IN.1, K1.9 (S), K2.9 (S)
G-OUT: C-AUDIO-OUT.2, C-AUDIO-OUT.4, K1.13, K2.13
GND: C3.2, C4.2, C5.2, CNX-ALIM.1, CNX-PUSH.1, CNX-TUNE1.2, CNX-TUNE2.2, IC3.7 (GND), JP5.2, RN1.1, T1.1 (E), T2.1 (E), X1.G1, X1.G2
L-FM: JP9.1, K1.6 (O)
L-MP3: C-AUDIO-IN.3, K1.8 (S)
L-OUT: C-AUDIO-OUT.1, K1.4
MISO: CNX-SPI.2, JP8.2, X1.14 (F)
MOSI: CNX-SPI.3, JP8.1, X1.1 (F)
unnamed: D2.A, K1.1, T2.3 (C)
unnamed: LED1.2, R2.2
unnamed: D1.A, K2.1, T1.3 (C)
unnamed: JP5.3, R1.2
unnamed: LED2.2, R3.2
unnamed: R4.2, T2.2 (B)
unnamed: R5.2, T1.2 (B)
PUSH: C3.1, CNX-PUSH.4, IC3.5 (I), RN3.3
R-FM: JP9.2, K2.6 (O)
R-MP3: C-AUDIO-IN.2, K2.8 (S)
R-OUT: C-AUDIO-OUT.3, K2.4
RST*: JP9.8, X1.24 (F)
SCK: CNX-SPI.1, JP8.3, X1.2 (F)
SCLK: C-I2C.1, JP4.1, Q1.3 (D), RN4.3, X1.12 (F)
SCLK-3: JP9.6, Q1.1 (S), RN2.5
SDIO: C-I2C.2, JP4.2, Q3.3 (D), RN4.5, X1.25 (F)
SDIO-3: JP9.5, Q3.1 (S), RN2.4
SEN*: JP9.7, X1.11 (F)
TURN-CCW: C4.1, CNX-PUSH.2, IC3.1 (I), RN3.5
TURN-CW: C5.1, CNX-PUSH.3, IC3.3 (I), RN3.4
VCC: C-FM-MP.2, C-MODE.6, CNX-ALIM.2, CNX-TUNE1.3, CNX-TUNE2.3, D1.C, D2.C, IC3.14 (VCC), JP5.1, K1.16 (2), K2.16 (2), LED1.1, LED2.1, RN3.1, RN4.1

Notes on the sheet:
Bus SPI
DAVID
Carte d'extension pour RADIAL-V - Connecteurs d'entrées/sorties. - Connecteur bus SPI
Commande du relais K1
Commande du relais K2
Bus I2C vers Slave 5v
Bus I2C vers Slave 3v3
Bus I2C vers Master
Bus I2C pour tests
Carte d'extension pour RADIAL-V - Commande des relais pour la sélection de l'audio (MP3 ou FM). - Connecteurs bus I2C (avec Level Shifter pour Slave sous 3v3)
Note: Ces deux connecteurs auraient pu être fusionnés.
