Sphinkie/Radial-V/sources/Radial-V/RotaryButton.cpp

/* ***********************************************************
 *  Gestion de Bouton de type Commutateur Rotatif
 *  
 ************************************************************* */
#include "Arduino.h"
#include "RotaryButton.h"
     
        
// ****************************************************************        
// Constructeur
//  On considère en dur qu'il y a 4 positions.
//  Donc, on initialise 4 entrées Digitales pour ce bouton.
// ****************************************************************        
Rotary::Rotary(int pin1, int pin2, int pin3, int pin4)
{
  // On initialise les variables
  Changed   = true;
  Value     = 4;    // default value = 4   [4:random 3:genre 2:year 1:fav]
  LastValue = 0;
  Pin1=pin1;
  Pin2=pin2;
  Pin3=pin3;
  Pin4=pin4;
  pinMode(pin1, INPUT);
  pinMode(pin2, INPUT);
  pinMode(pin3, INPUT);
  pinMode(pin4, INPUT);
  // Note: Serial n'est pas encore initialisé!
}

// ****************************************************************        
// Constructeur pour 2 positions.
// ****************************************************************        
Rotary::Rotary(int pin1, int pin2)
{
  // On initialise les variables
  Changed   = true;
  Value     = 0;    // default value = 1
  LastValue = 0;
  Pin1=pin1;
  Pin2=pin2;
  Pin3=0;
  Pin4=0;
  pinMode(pin1, INPUT);
  pinMode(pin2, INPUT);
  // Note: Serial n'est pas encore initialisé!
}
       
        
// ****************************************************************        
// Normalement, une seule de ces positions est active à un instant donné.
// On renvoie une valeur de 1 à 4 
// ****************************************************************        
int Rotary::readPosition()
{
  LastValue=Value;
  Value=0;
  if (digitalRead(Pin1)==HIGH) Value=1;
  if (digitalRead(Pin2)==HIGH) Value=2;
  if ((Pin3!=0) && (digitalRead(Pin3)==HIGH)) Value=3;
  if ((Pin4!=0) && (digitalRead(Pin4)==HIGH)) Value=4;
  if (Value != LastValue) Changed=true;
  return Value;
}

// ****************************************************************        
// On renvoie la position lue la plus récente (valeur de 1 à 4)
// ****************************************************************        
int Rotary::getValue()
{
  Changed = false;
  return Value;
}

// ****************************************************************        
// On renvoie la position précédente (valeur de 1 à 4)
// ****************************************************************        
int Rotary::getLastValue()
{
  return LastValue;
}


// ****************************************************************        
// Indique si le bouton a changé de position depuis le dernier appel à la fonction
// ****************************************************************        
bool Rotary::hasChanged()
{
  bool ChangeStatus = Changed;
  Changed = false;
  return ChangeStatus;
}
